LS120nz/OD-PT74-IC-Tester/docs/images/branding/image.png

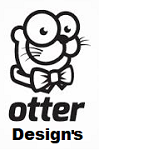
docs/images/branding/image.png
