LS120nz/OD-PT74-IC-Tester/docs/images/branding/png/otter_128.png

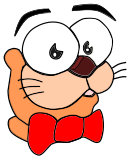
docs/images/branding/png/otter_128.png
