LS120nz/OD-PT74-IC-Tester/docs/images/branding/svga/OtterDesigns_FullColour.jpg

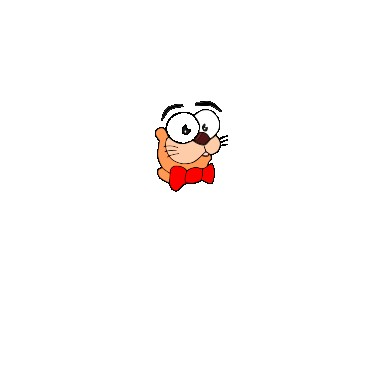
docs/images/branding/svga/OtterDesigns_FullColour.jpg
