LS120nz/OD-PT74-IC-Tester/docs/images/case labels/qr-back.png

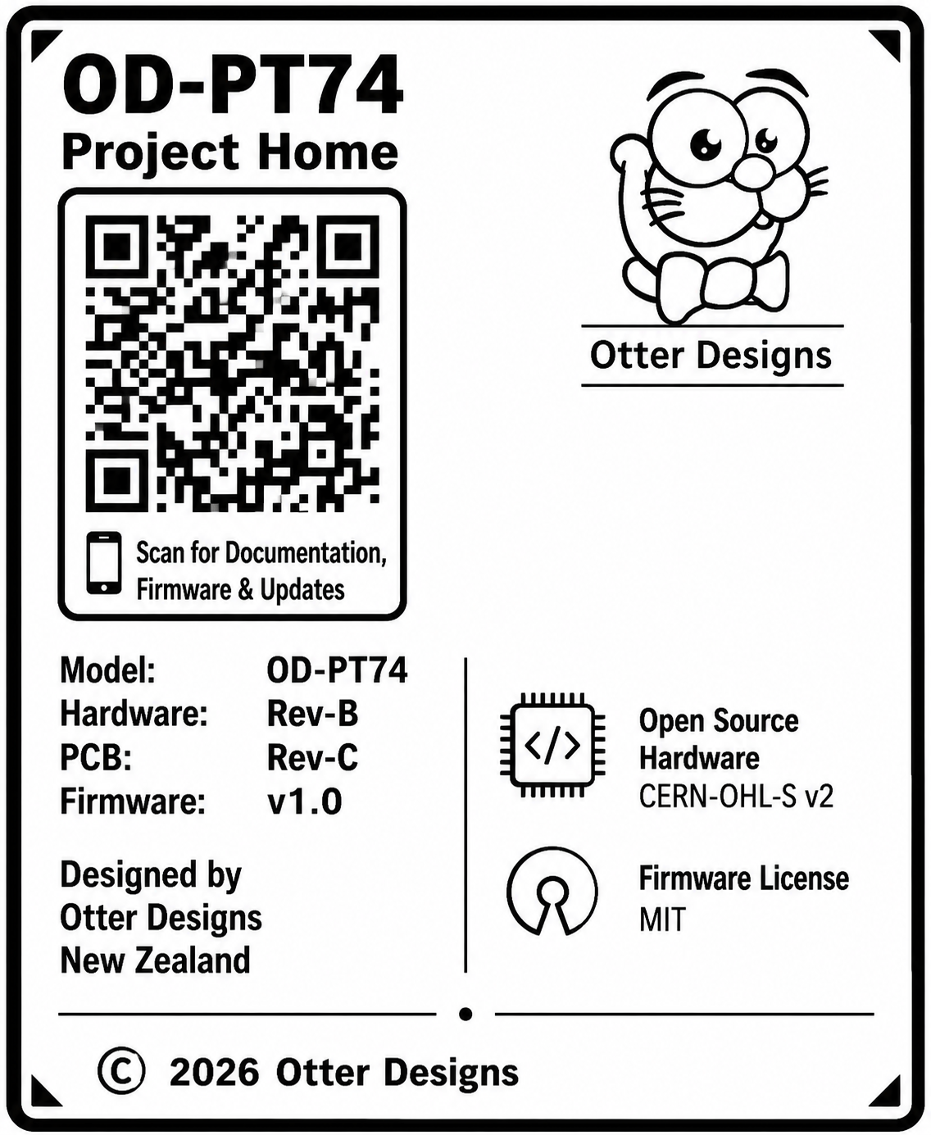
docs/images/case labels/qr-back.png
