LS120nz/OD-PT74-IC-Tester/docs/images/firmware/03-usb-settings.jpg

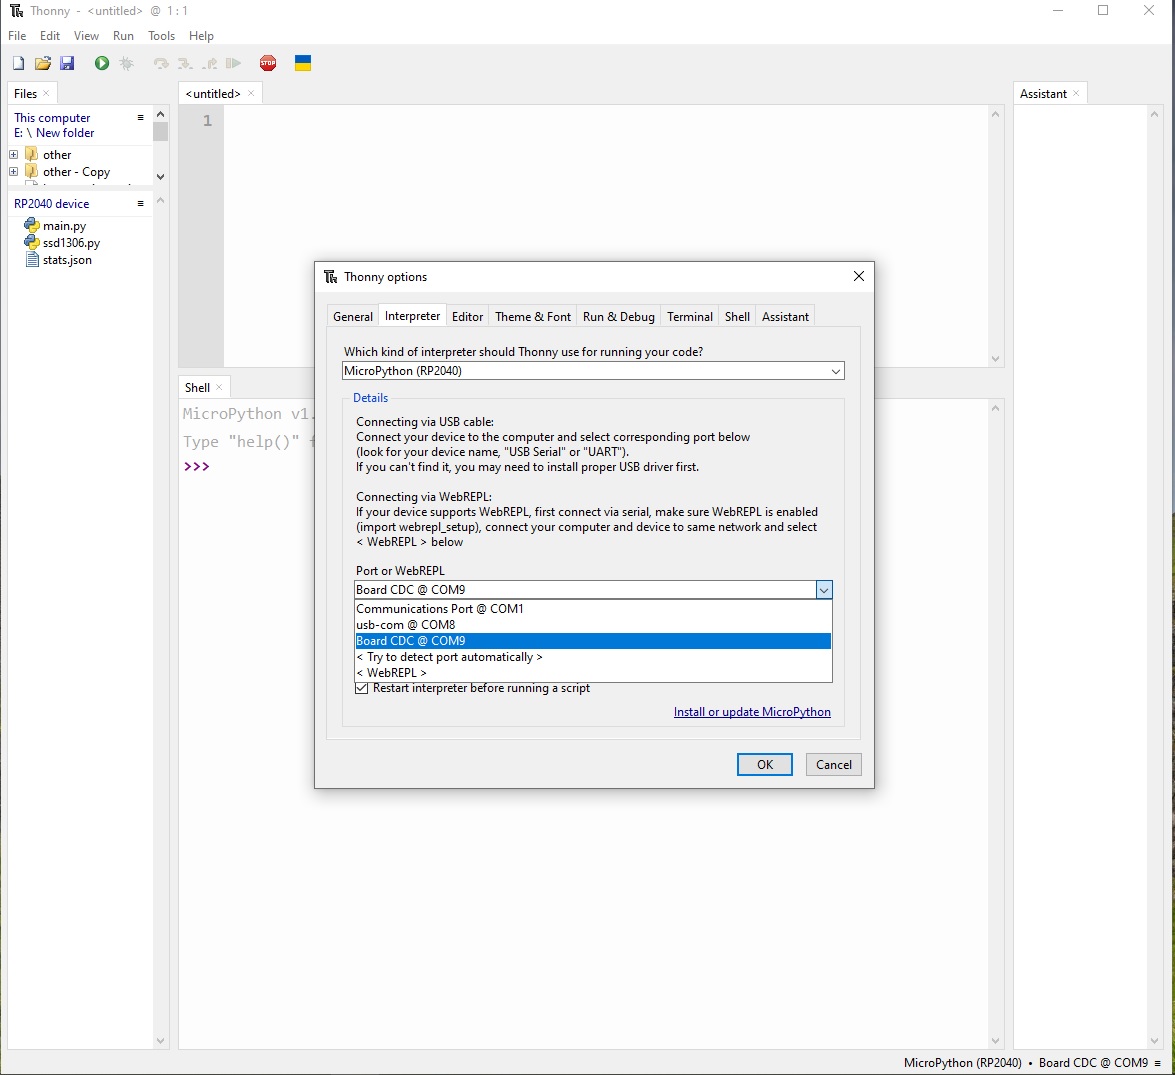
docs/images/firmware/03-usb-settings.jpg
