LS120nz/OD-PT74-IC-Tester/docs/images/firmware/24-files on PR2040.jpg

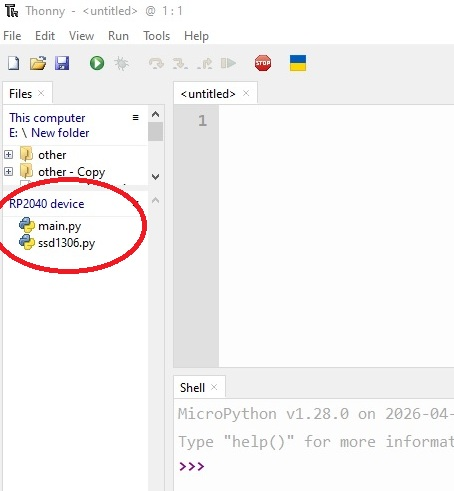
docs/images/firmware/24-files on PR2040.jpg
