LS120nz/OD-PT74-IC-Tester/docs/images/hardware/case label.jpg

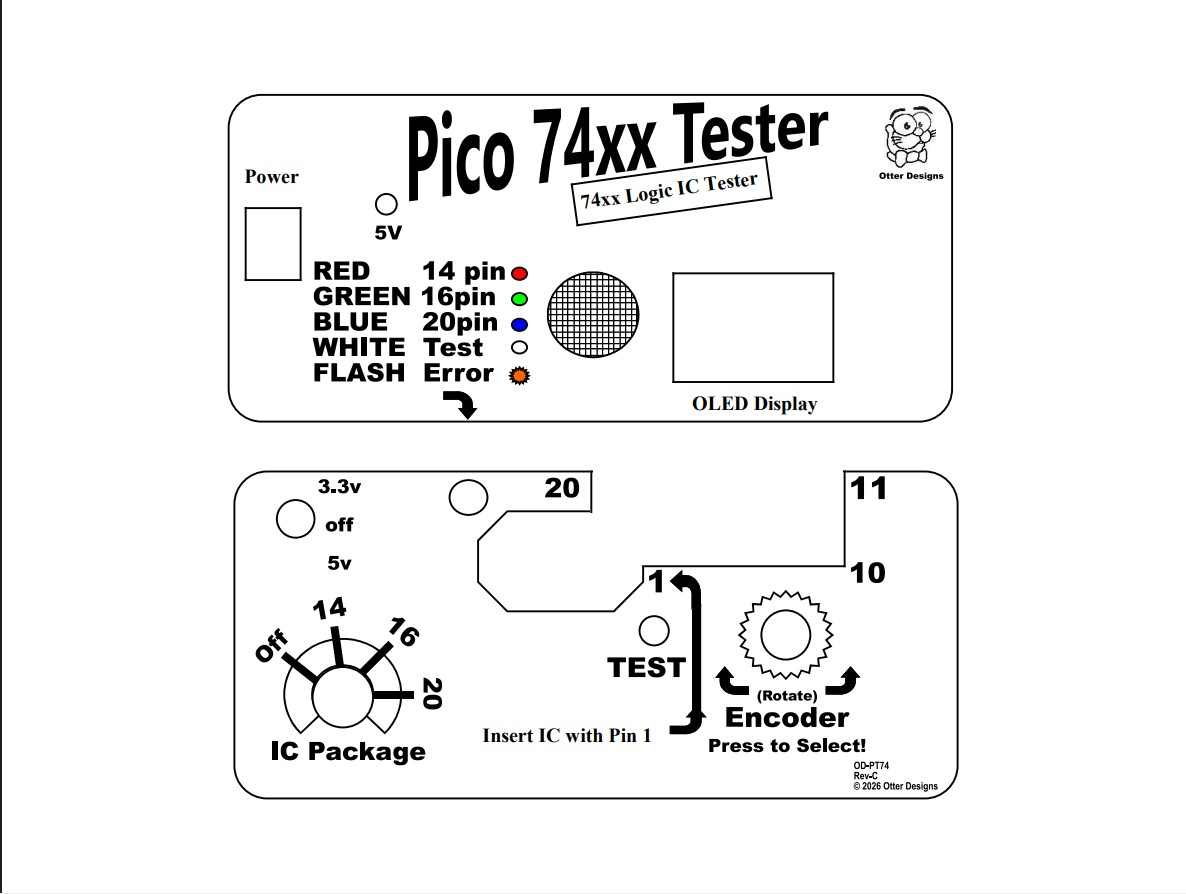
docs/images/hardware/case label.jpg
