LS120nz/OD-PT74-IC-Tester/docs/images/hardware/enclosure.jpg

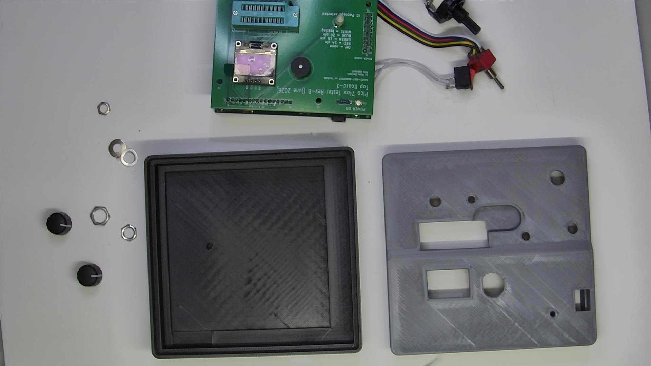
docs/images/hardware/enclosure.jpg
