LS120nz/OD-PT74-IC-Tester/docs/images/hardware/internal-view.jpg

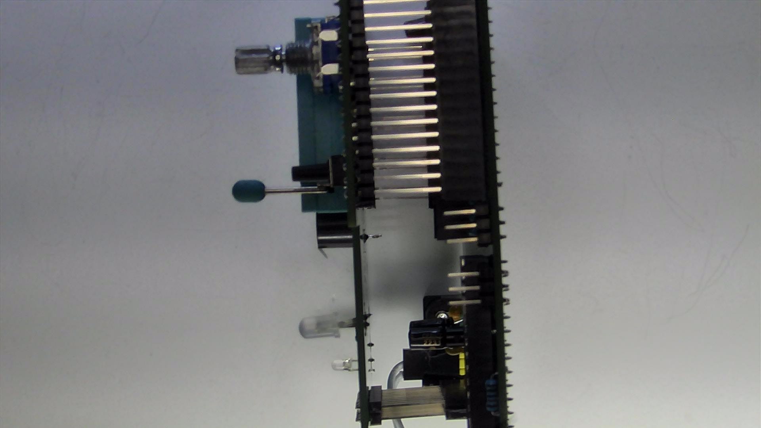
docs/images/hardware/internal-view.jpg
