LS120nz/OD-PT74-IC-Tester/hardware/OD-PT74 - Rev-C/Base Board/Images/OD-PT74_Rev-C_Base_Board-3D.png

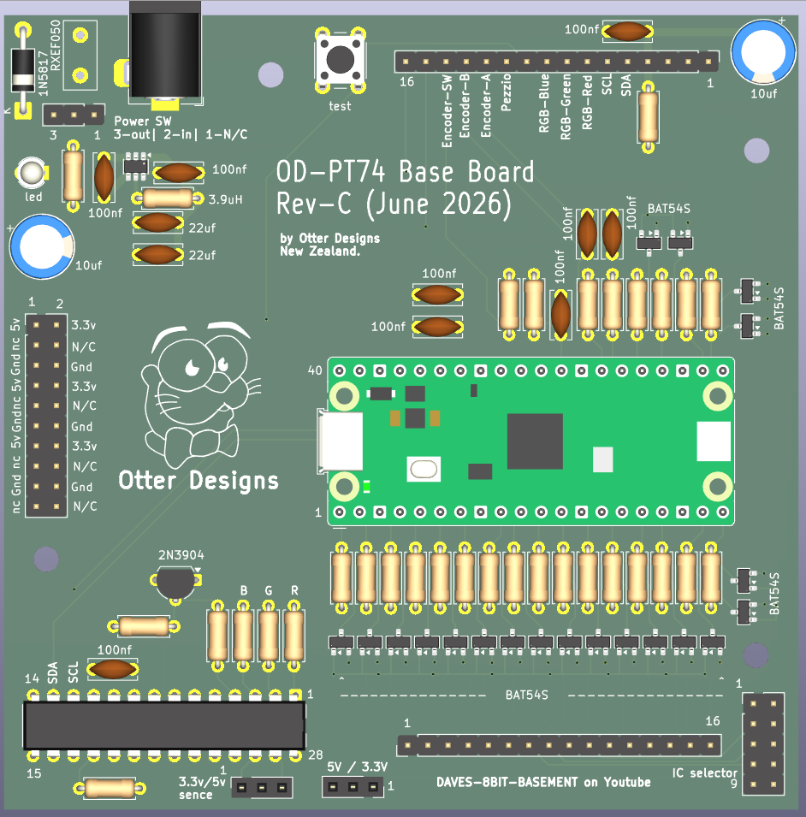
hardware/OD-PT74 - Rev-C/Base Board/Images/OD-PT74_Rev-C_Base_Board-3D.png
