LS120nz/OD-PT74-IC-Tester/hardware/OD-PT74 - Rev-C/Top Board/Images/3d top board.png

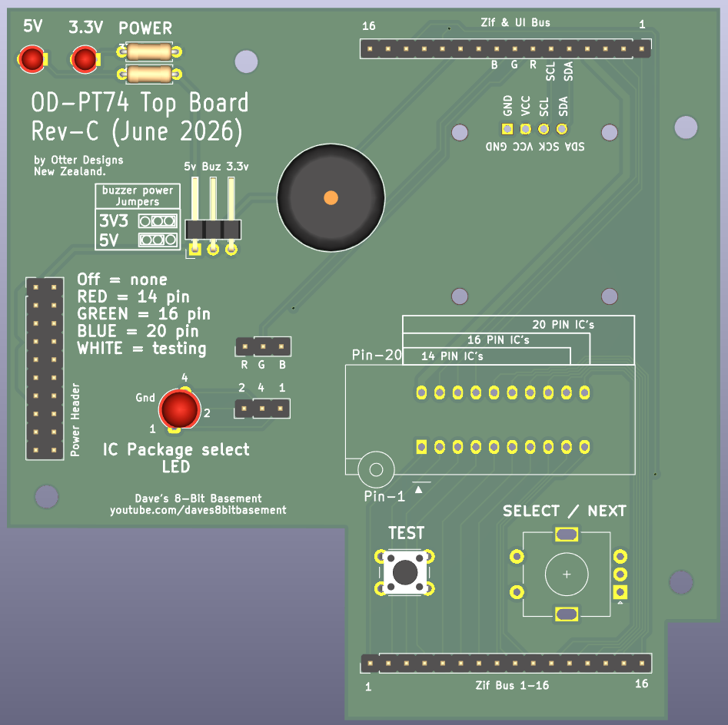
hardware/OD-PT74 - Rev-C/Top Board/Images/3d top board.png
