LS120nz/OD-PT74-IC-Tester/hardware/OD-PT74 - Rev-C/Top Board/Images/top board schematics.png

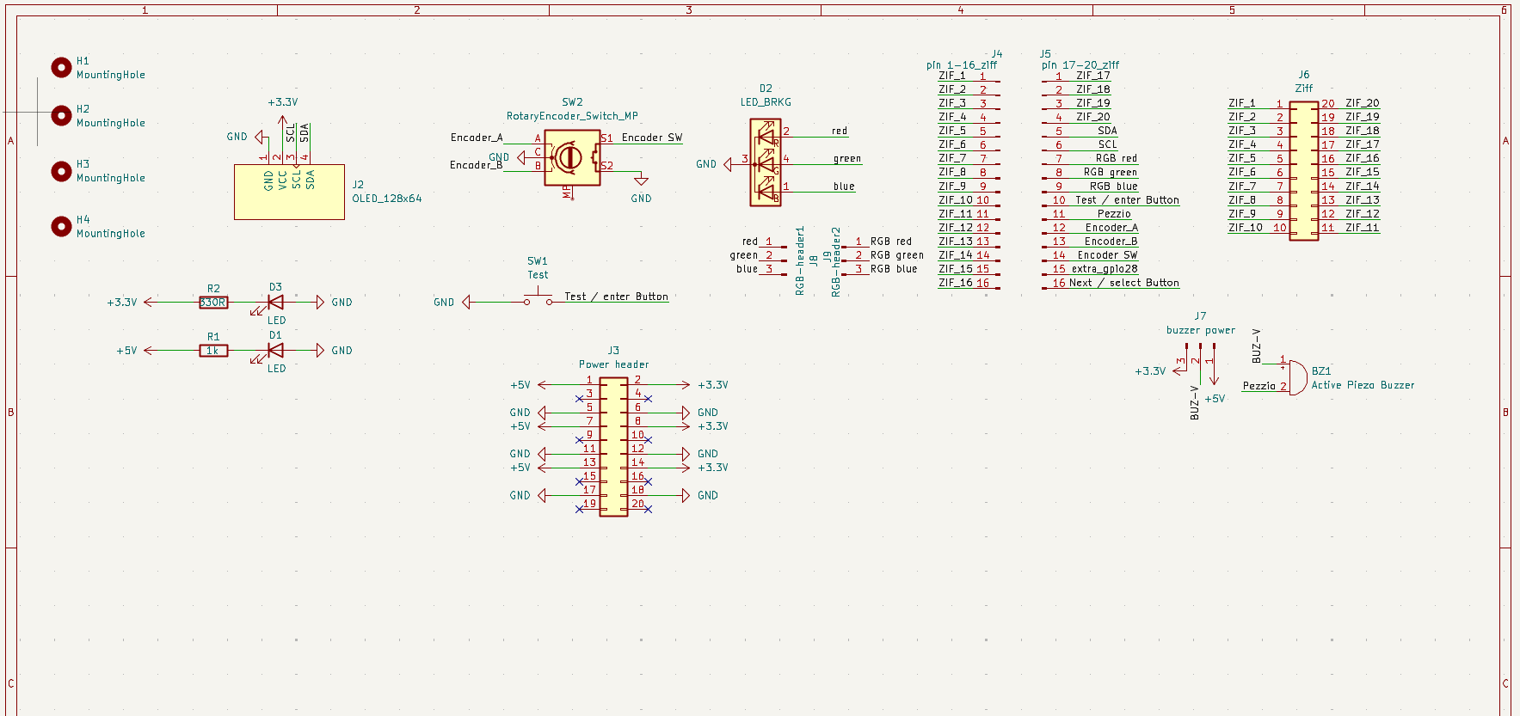
hardware/OD-PT74 - Rev-C/Top Board/Images/top board schematics.png
