LS120nz/OD-PT74-IC-Tester/images/enclosure/base-cad2.jpg

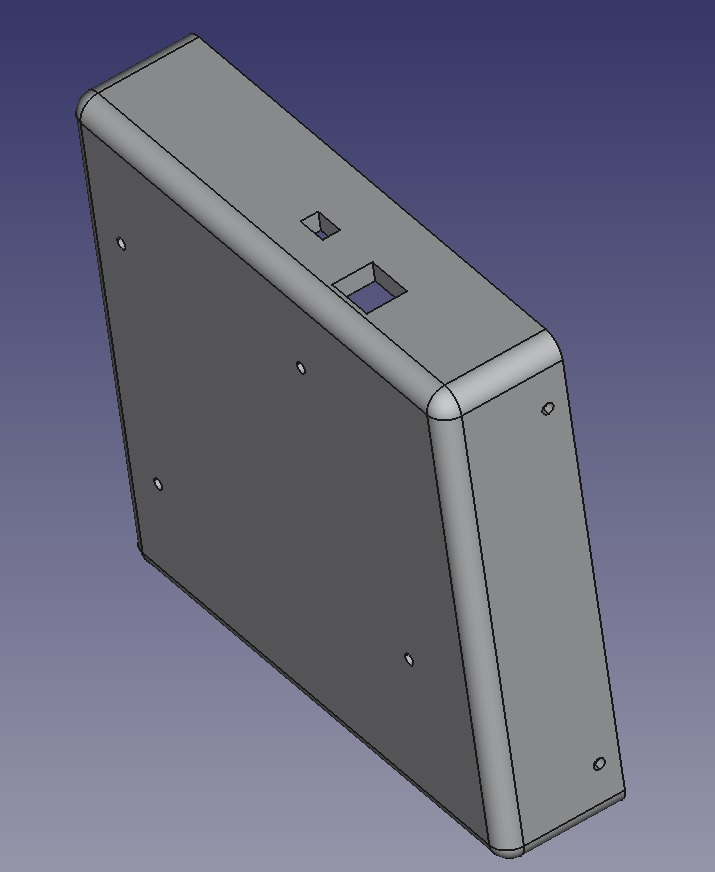
images/enclosure/base-cad2.jpg
