LS120nz/OD-PT74-IC-Tester/images/enclosure/base-cad.jpg

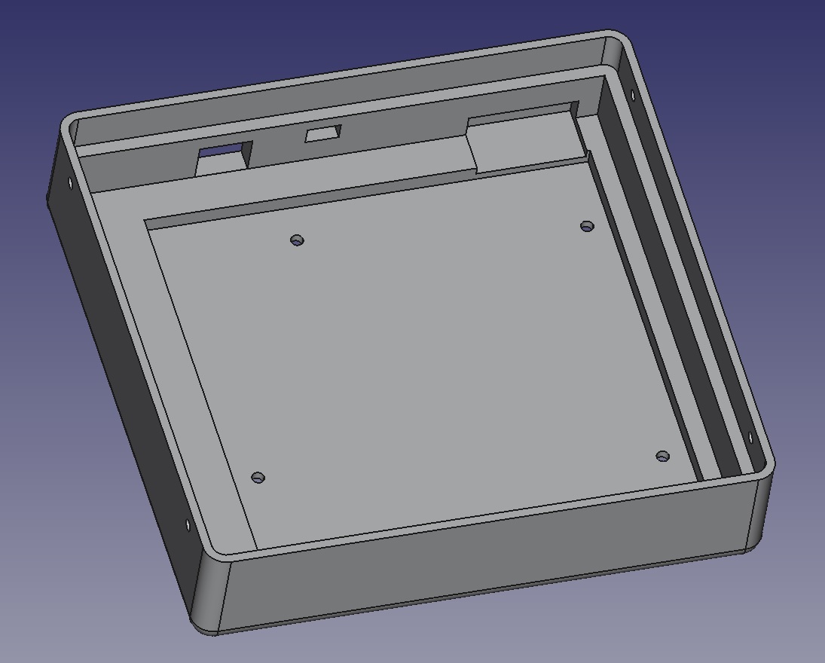
images/enclosure/base-cad.jpg
