LS120nz/OD-PT74-IC-Tester/images/enclosure/top-cad2.jpg

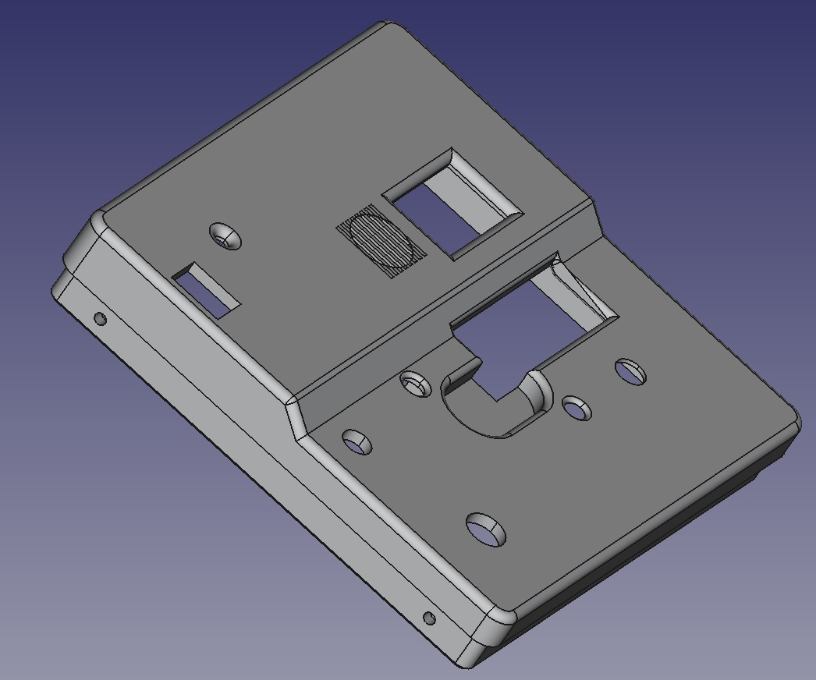
images/enclosure/top-cad2.jpg
