LS120nz/OD-PT74-IC-Tester/images/enclosure/top-cad3.jpg

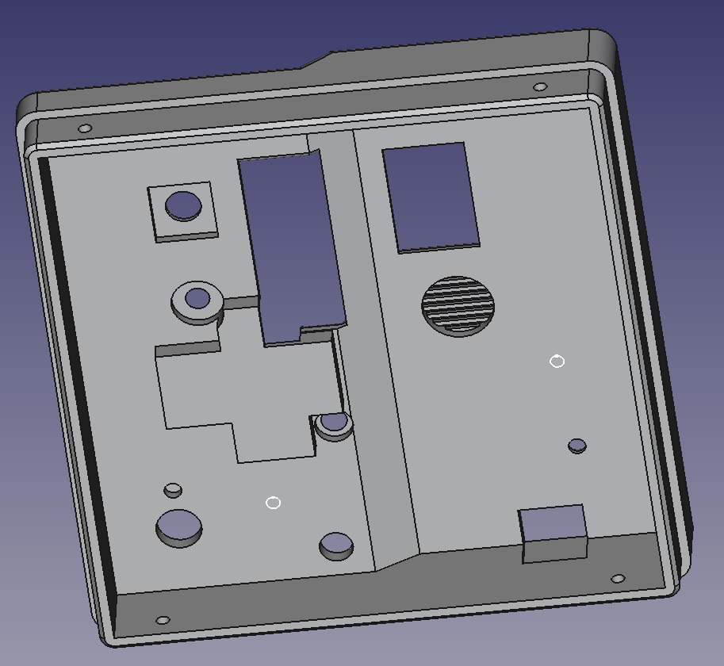
images/enclosure/top-cad3.jpg
