LS120nz/OD-PT74-IC-Tester/images/enclosure/top-cad.jpg

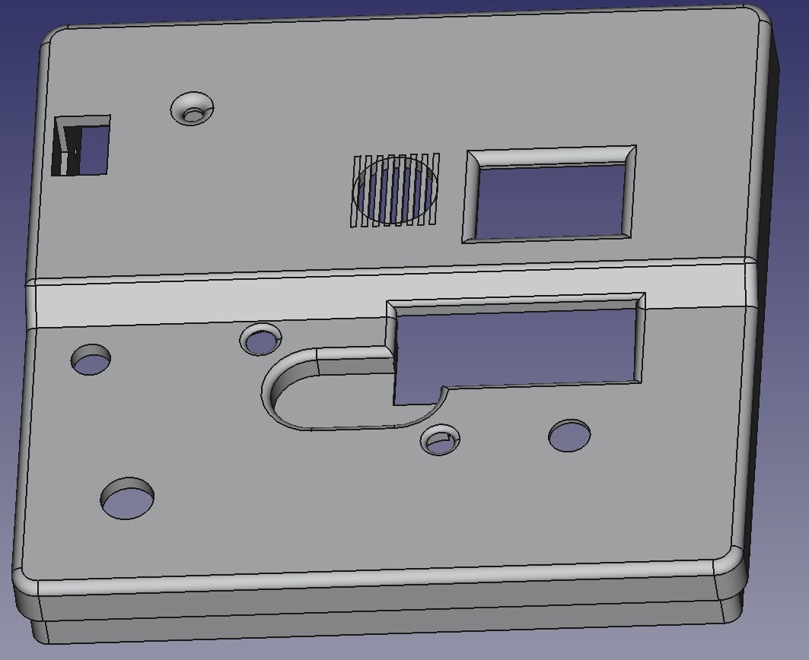
images/enclosure/top-cad.jpg
