LS120nz/OD-PT74-IC-Tester/images/pcb-back.jpg

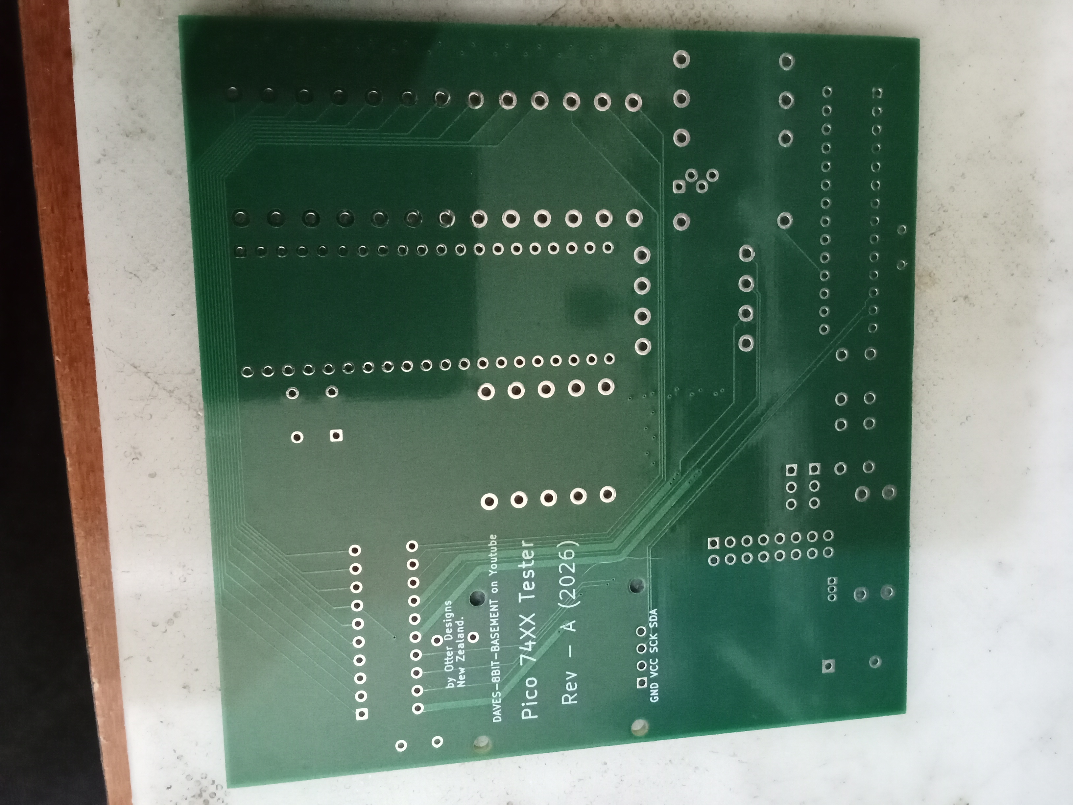
images/pcb-back.jpg
