LS120nz/OD-PT74-IC-Tester/images/pcb-front.jpg

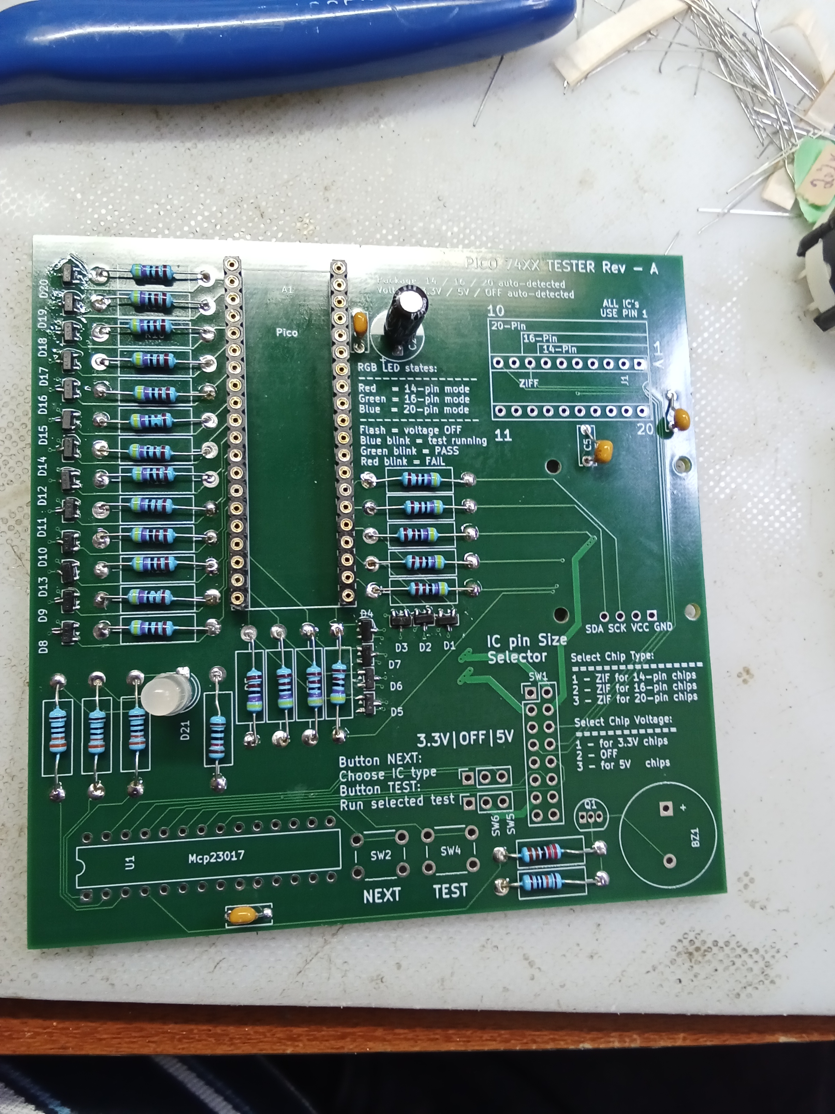
images/pcb-front.jpg
