LS120nz/OD-PT74-IC-Tester/images/RevB-3d-board-top.png

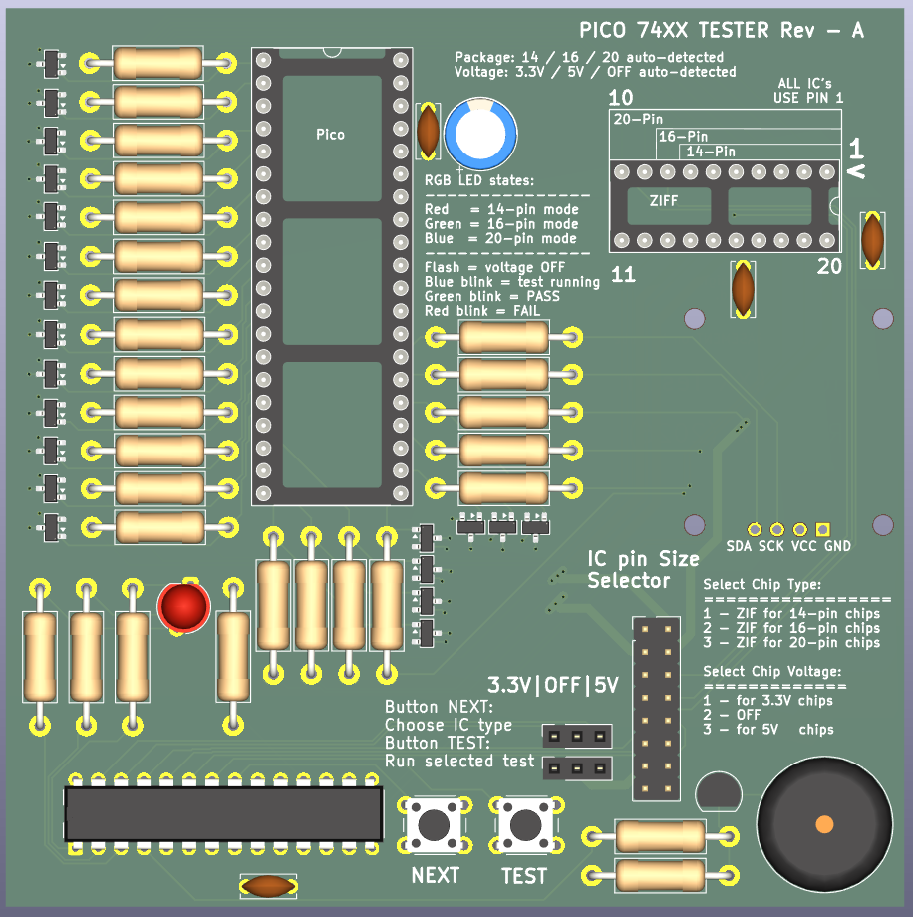
images/RevB-3d-board-top.png
