LS120nz/OD-PT74-IC-Tester/images/top-back-3d.png

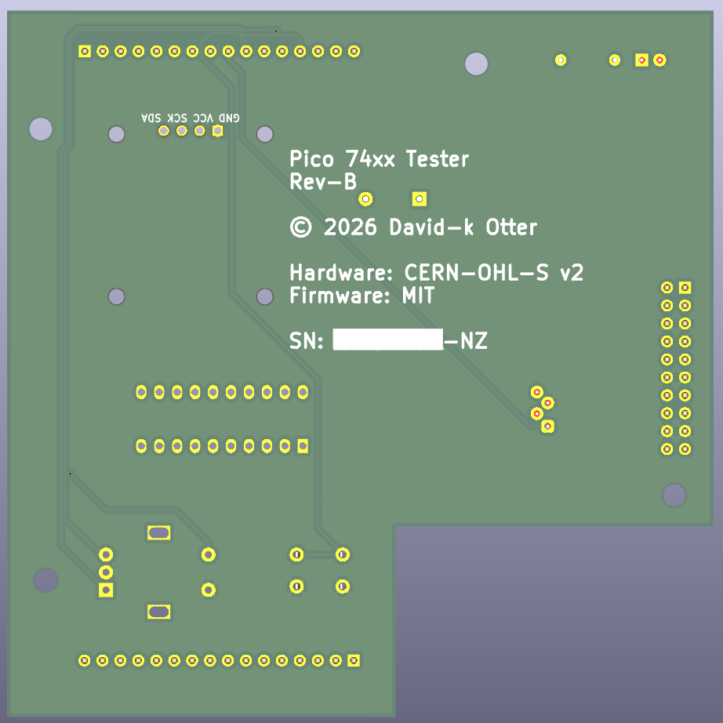
images/top-back-3d.png
