LS120nz/OD-PT74-IC-Tester/images/top-front-3d.png

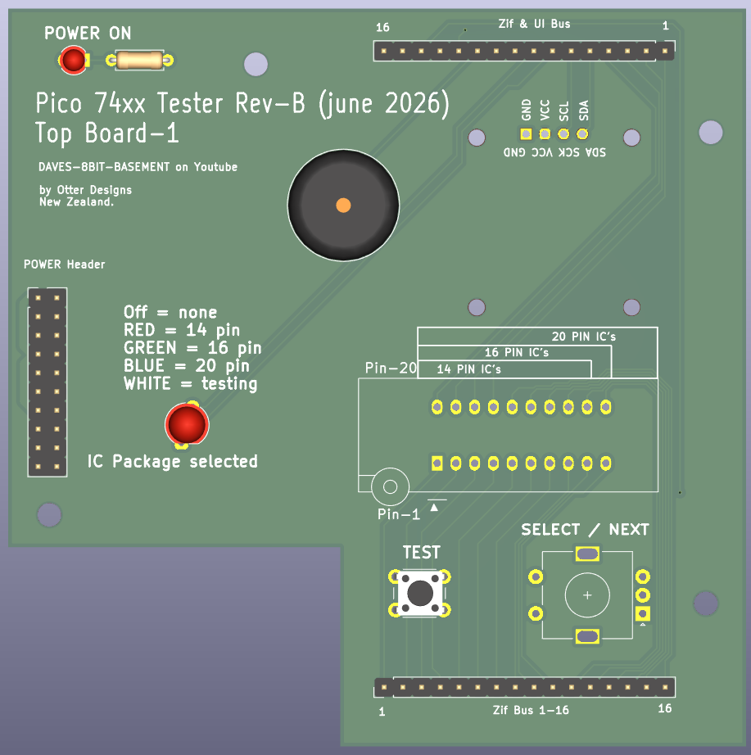
images/top-front-3d.png
