LS120nz/OD-PT74-IC-Tester/images/top-kicad-drawing.png

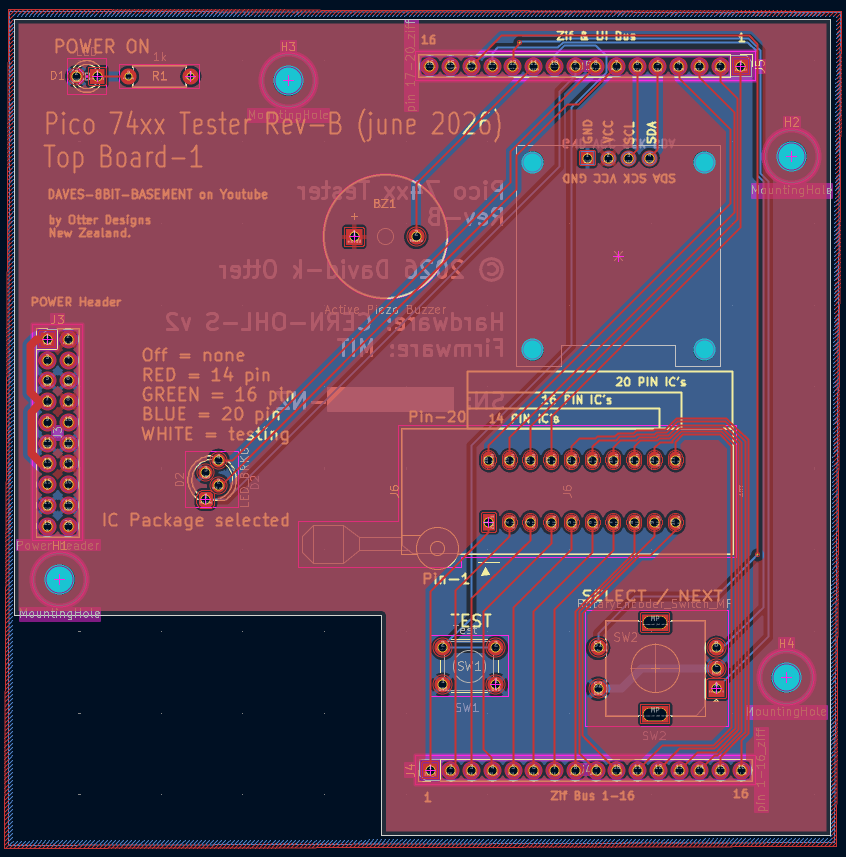
images/top-kicad-drawing.png
