LS120nz/OD-PT74-IC-Tester/docs/images/build/22-topboard-parts.jpg

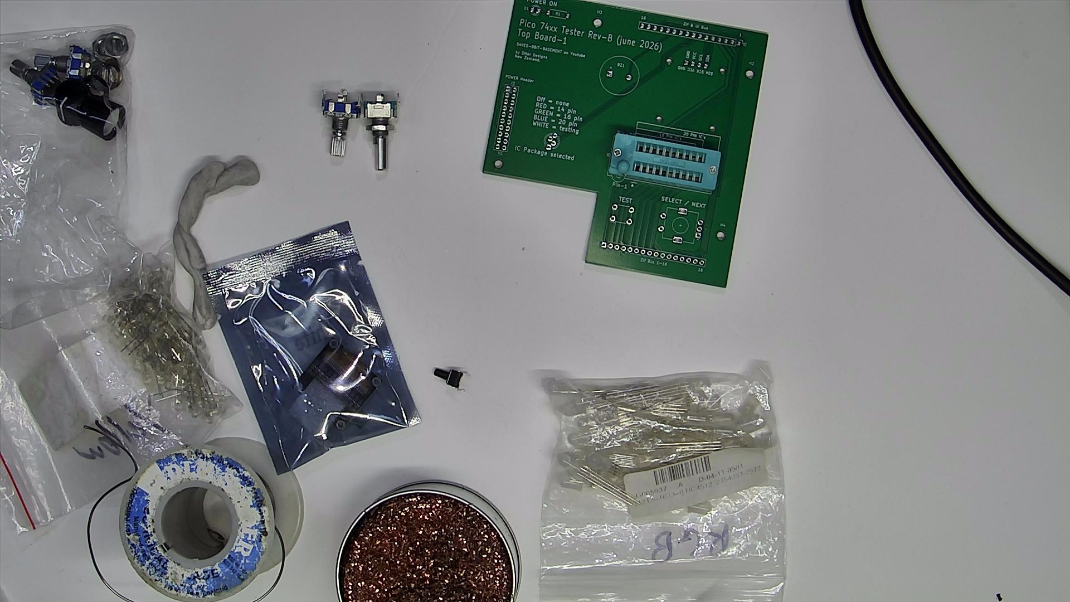
docs/images/build/22-topboard-parts.jpg
