LS120nz/OD-PT74-IC-Tester/docs/images/build/06-attach header pins.jpg

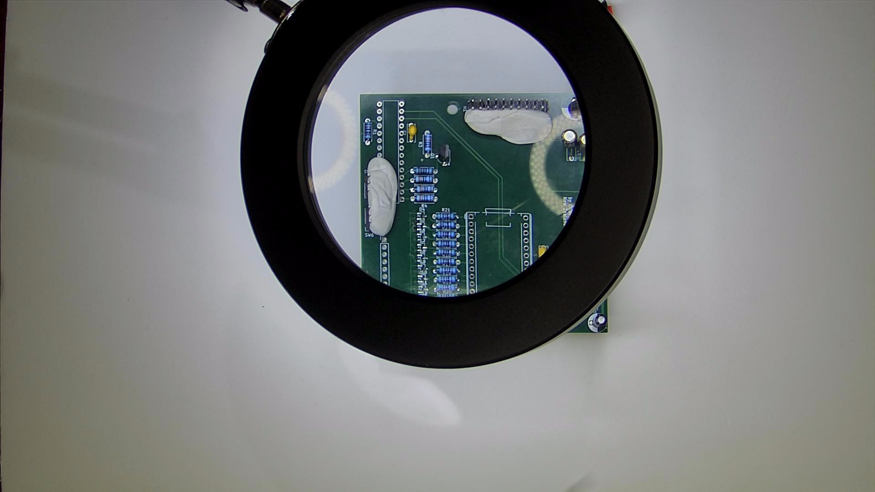
docs/images/build/06-attach header pins.jpg
