LS120nz/OD-PT74-IC-Tester/docs/images/build/08-baseboard-headers.jpg

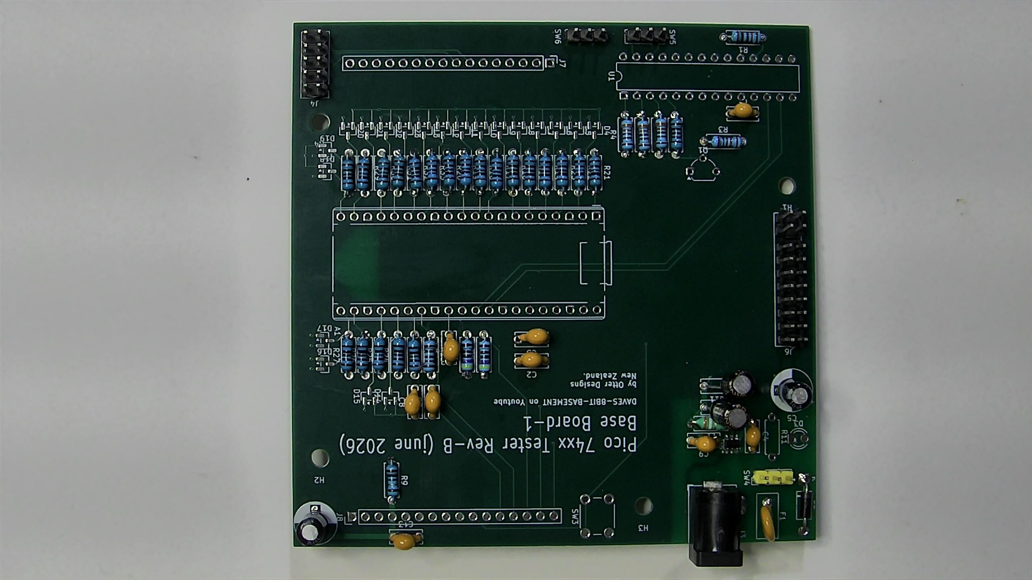
docs/images/build/08-baseboard-headers.jpg
