LS120nz/OD-PT74-IC-Tester/docs/images/build/09-first-bat-1.jpg

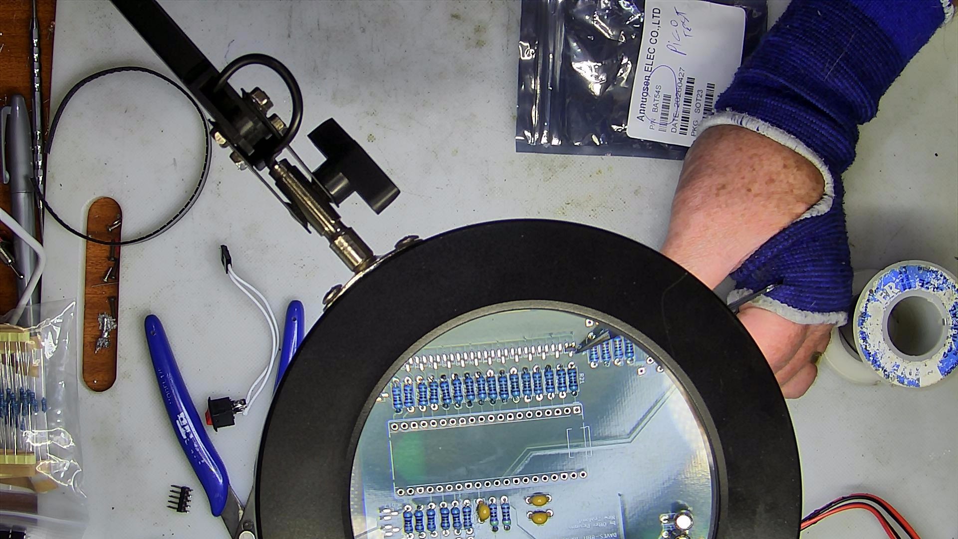
docs/images/build/09-first-bat-1.jpg
