LS120nz/OD-PT74-IC-Tester/docs/images/build/10-fist-bat-2.jpg

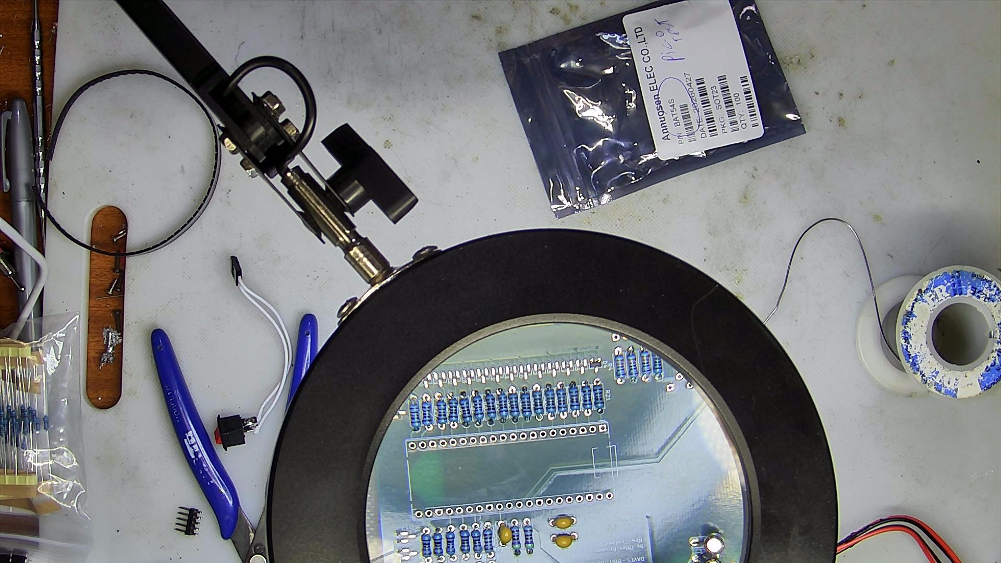
docs/images/build/10-fist-bat-2.jpg
