LS120nz/OD-PT74-IC-Tester/docs/images/build/11-bat-4.jpg

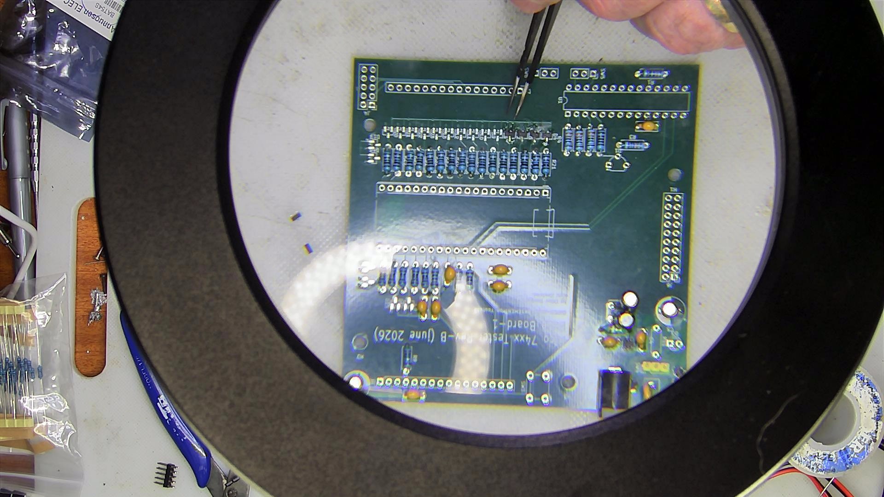
docs/images/build/11-bat-4.jpg
