LS120nz/OD-PT74-IC-Tester/docs/images/build/13-bat-attach-2_3.jpg

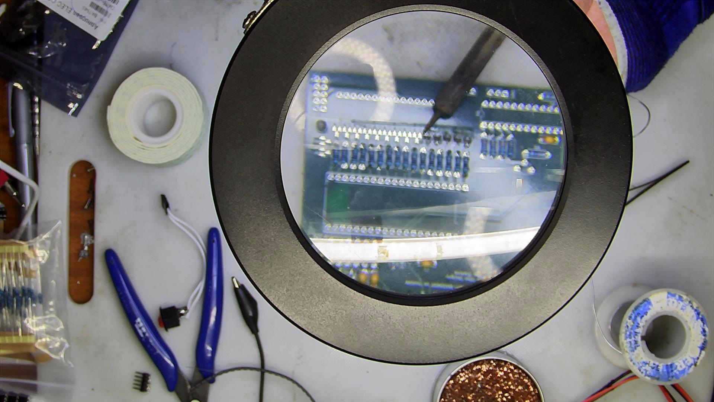
docs/images/build/13-bat-attach-2_3.jpg
