LS120nz/OD-PT74-IC-Tester/docs/images/build/14-bat-5-strighten.jpg

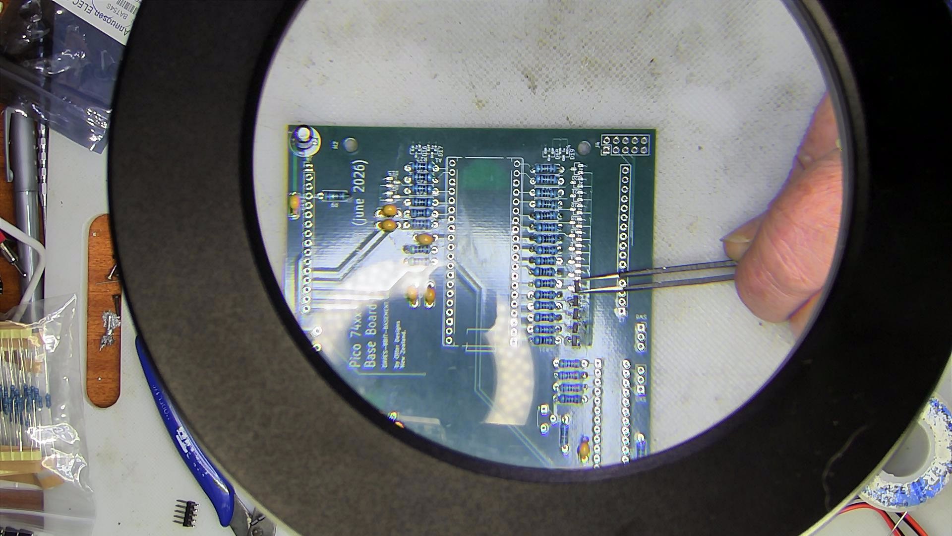
docs/images/build/14-bat-5-strighten.jpg
