LS120nz/OD-PT74-IC-Tester/docs/images/build/15-baseboard-most-bats.jpg

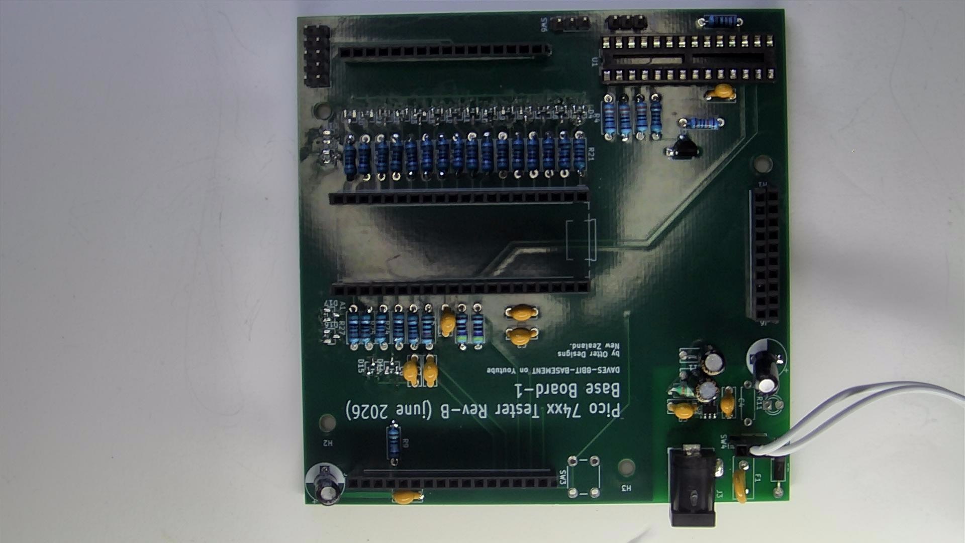
docs/images/build/15-baseboard-most-bats.jpg
