LS120nz/OD-PT74-IC-Tester/docs/images/build/21-blank-topboard.jpg

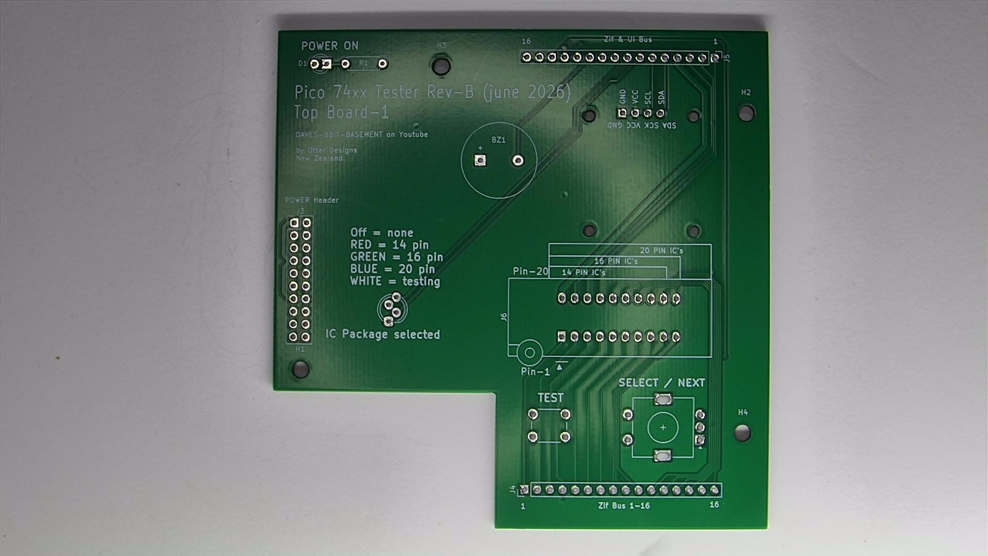
docs/images/build/21-blank-topboard.jpg
