LS120nz/OD-PT74-IC-Tester/docs/images/build/23-topboard-zif-solder.jpg

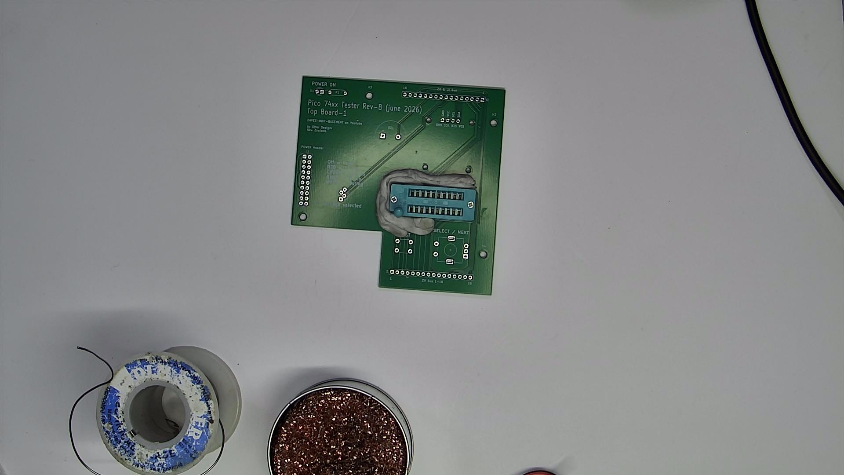
docs/images/build/23-topboard-zif-solder.jpg
