LS120nz/OD-PT74-IC-Tester/docs/images/build/24-topboard-rgb.jpg

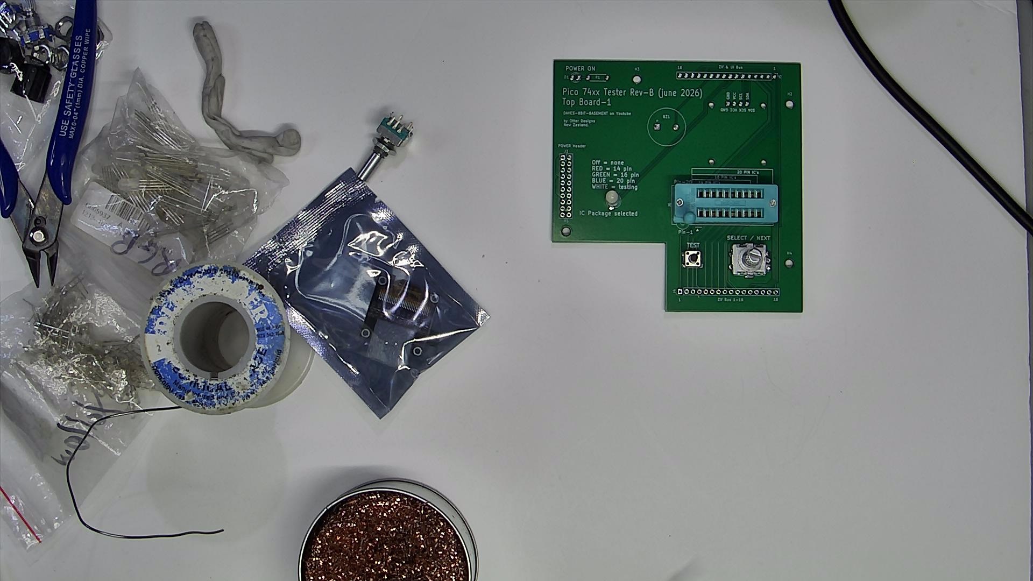
docs/images/build/24-topboard-rgb.jpg
