LS120nz/OD-PT74-IC-Tester/docs/images/build/26-oled-tape.jpg

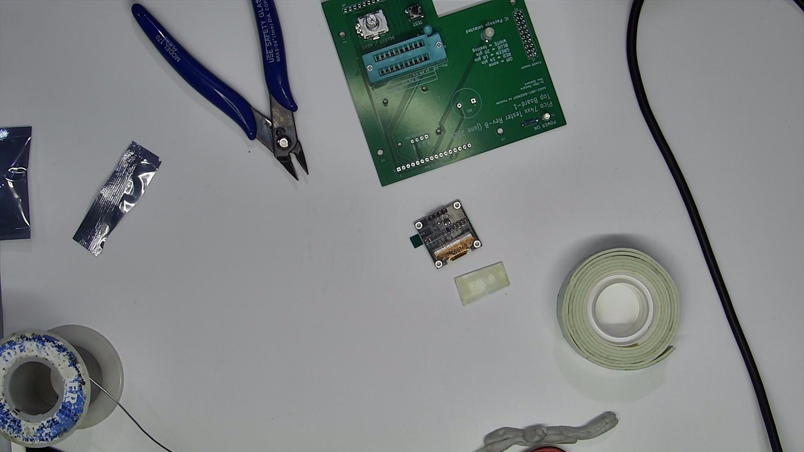
docs/images/build/26-oled-tape.jpg
