LS120nz/OD-PT74-IC-Tester/docs/images/build/27-oled-mount-tap.jpg

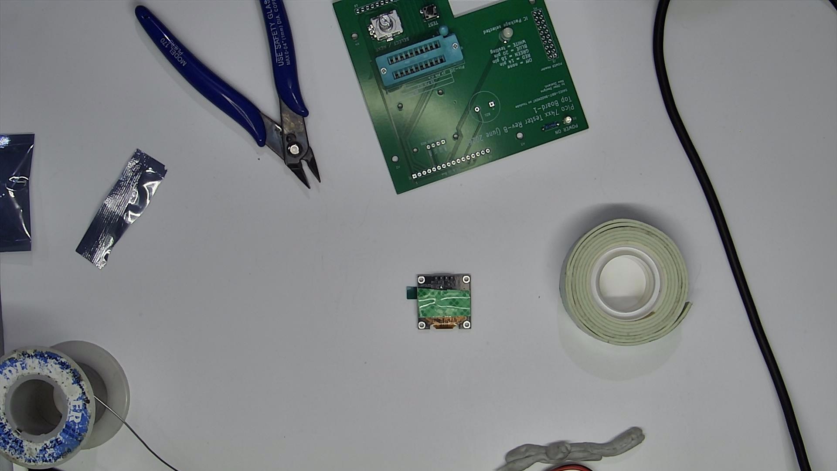
docs/images/build/27-oled-mount-tap.jpg
