LS120nz/OD-PT74-IC-Tester/docs/images/build/28-oled-side-view.jpg

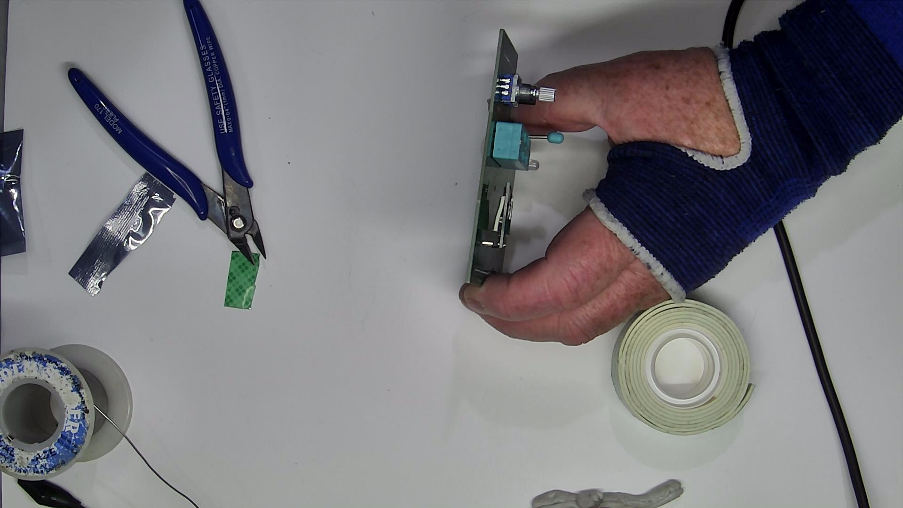
docs/images/build/28-oled-side-view.jpg
