LS120nz/OD-PT74-IC-Tester/docs/images/build/29-oled-side-mount.jpg

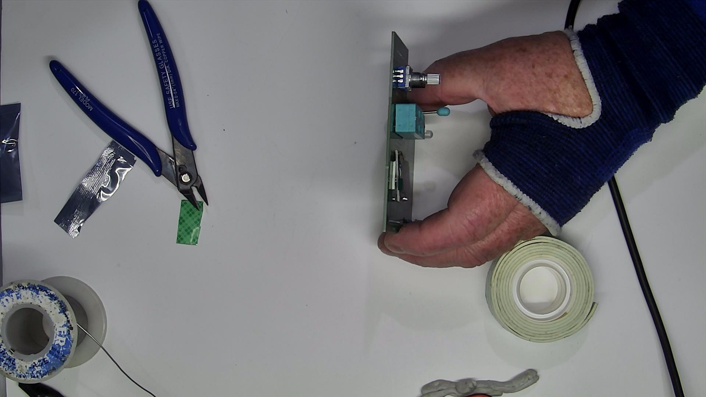
docs/images/build/29-oled-side-mount.jpg
