LS120nz/OD-PT74-IC-Tester/docs/images/build/30-power-led.jpg

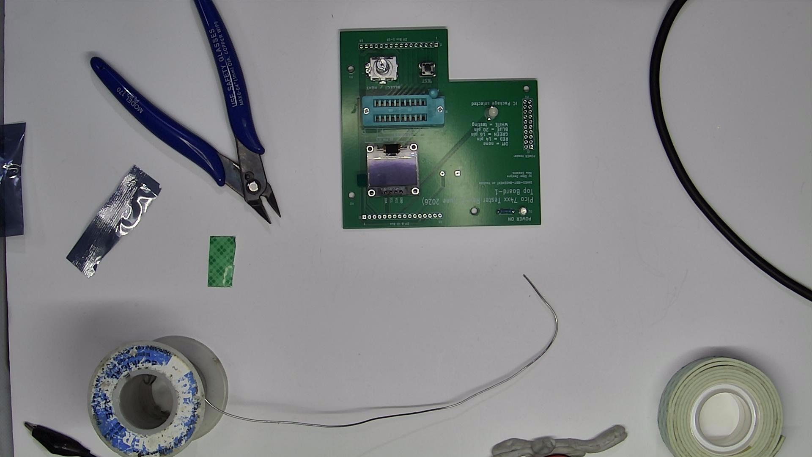
docs/images/build/30-power-led.jpg
