LS120nz/OD-PT74-IC-Tester/docs/images/build/31-topboard-header-aligen.jpg

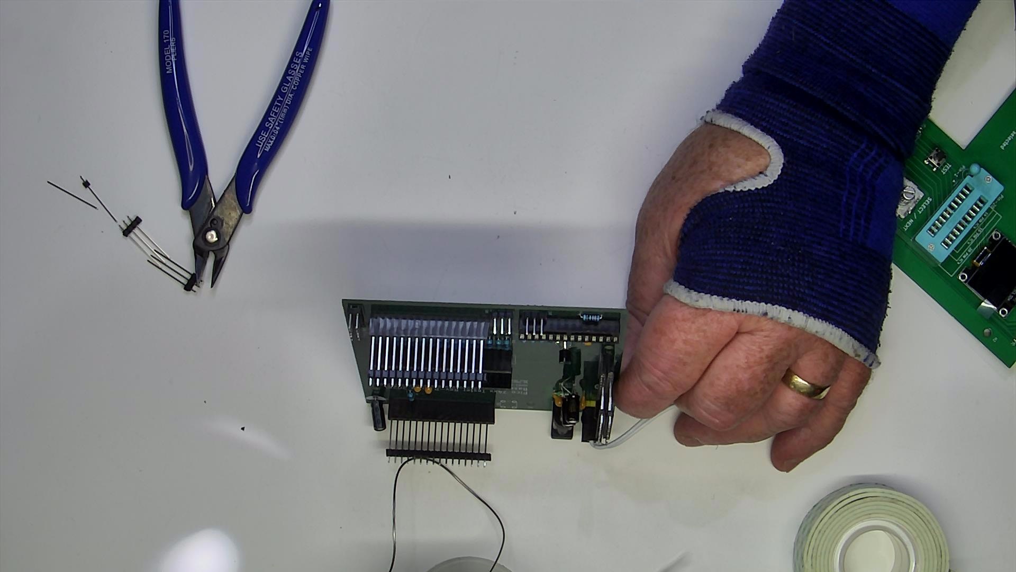
docs/images/build/31-topboard-header-aligen.jpg
