LS120nz/OD-PT74-IC-Tester/docs/images/build/32-topboard-hearer-aligen2.jpg

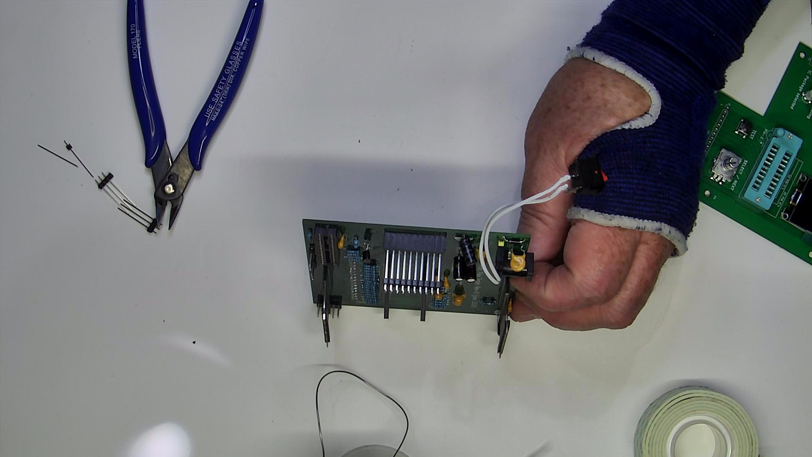
docs/images/build/32-topboard-hearer-aligen2.jpg
