LS120nz/OD-PT74-IC-Tester/docs/images/build/33-topboard aligen-on-pins.jpg

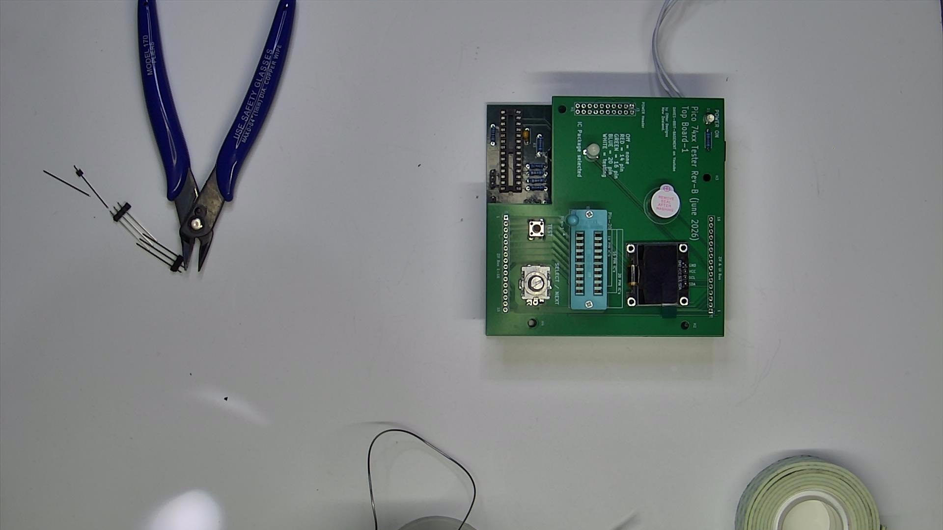
docs/images/build/33-topboard aligen-on-pins.jpg
