LS120nz/OD-PT74-IC-Tester/docs/images/build/34-topboard-buzzer-and-pins soldered.jpg

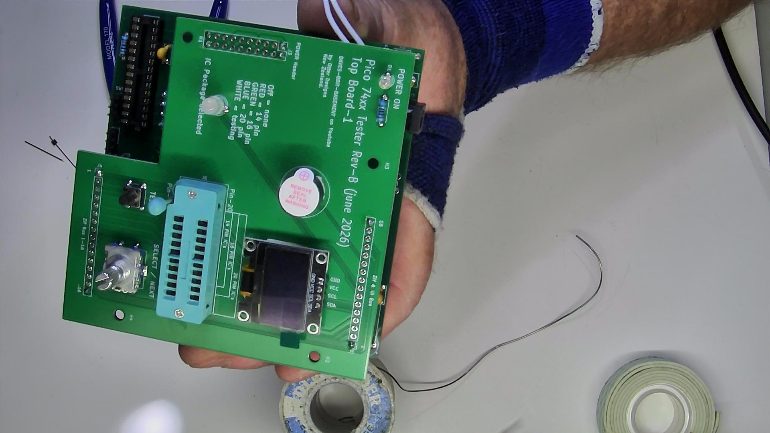
docs/images/build/34-topboard-buzzer-and-pins soldered.jpg
