LS120nz/OD-PT74-IC-Tester/docs/images/build/36-bottom-topboard.jpg

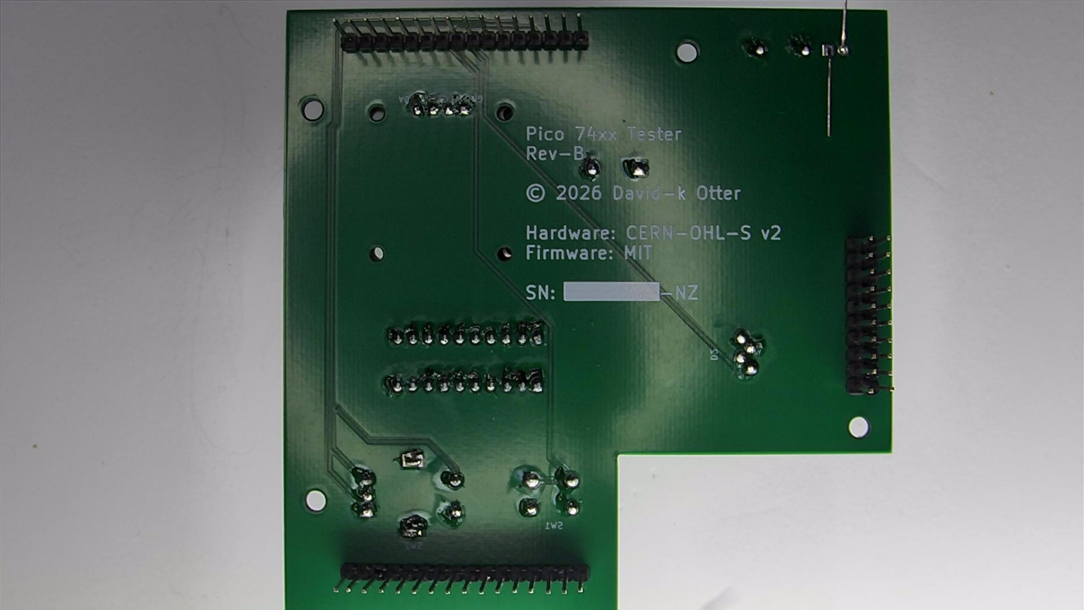
docs/images/build/36-bottom-topboard.jpg
