LS120nz/OD-PT74-IC-Tester/docs/images/build/38-selector-cables.jpg

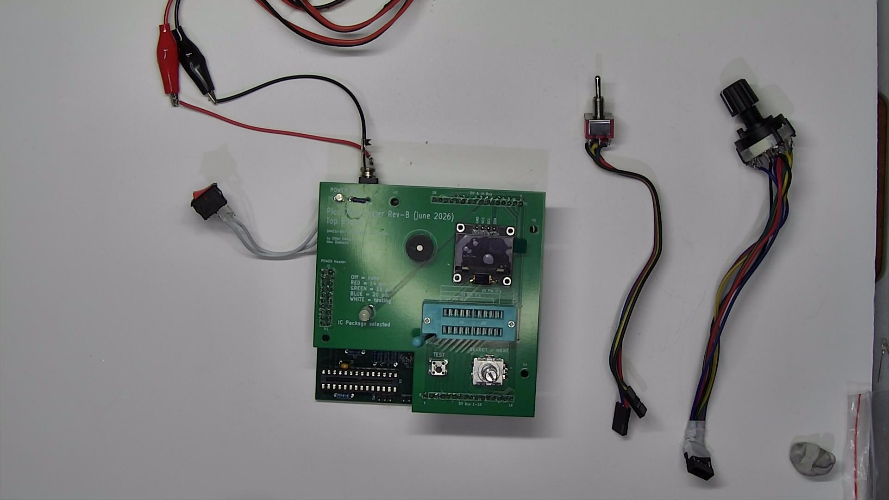
docs/images/build/38-selector-cables.jpg
