LS120nz/OD-PT74-IC-Tester/docs/images/build/39-selector-cables-closeup.jpg

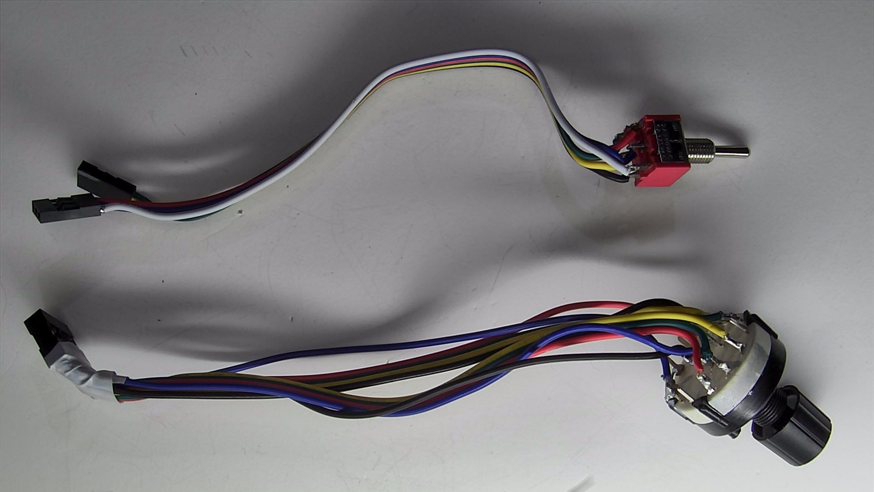
docs/images/build/39-selector-cables-closeup.jpg
