LS120nz/OD-PT74-IC-Tester/docs/images/build/40-baseboard-plugged-up.jpg

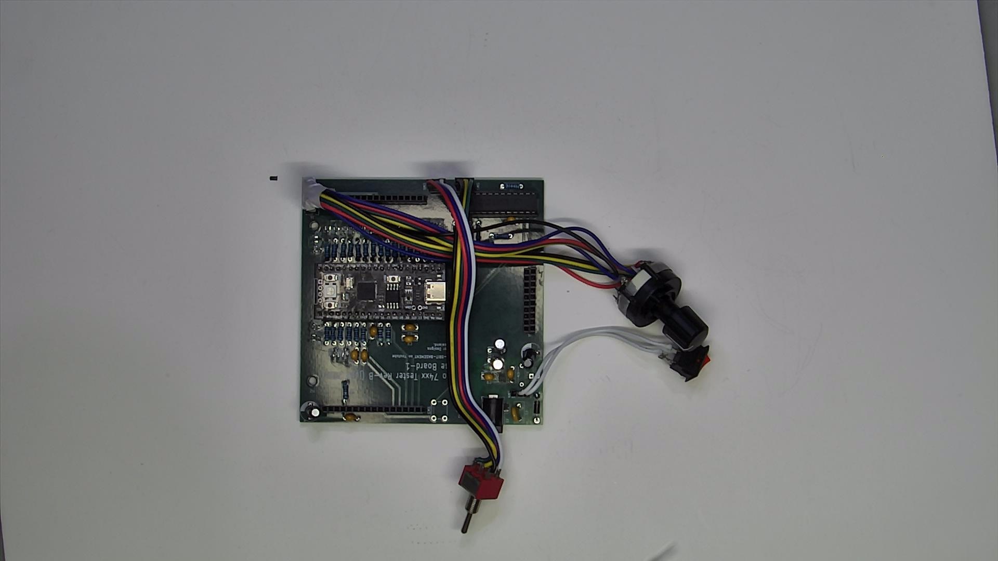
docs/images/build/40-baseboard-plugged-up.jpg
