LS120nz/OD-PT74-IC-Tester/docs/images/build/41-baseboard-plugged-up-side.jpg

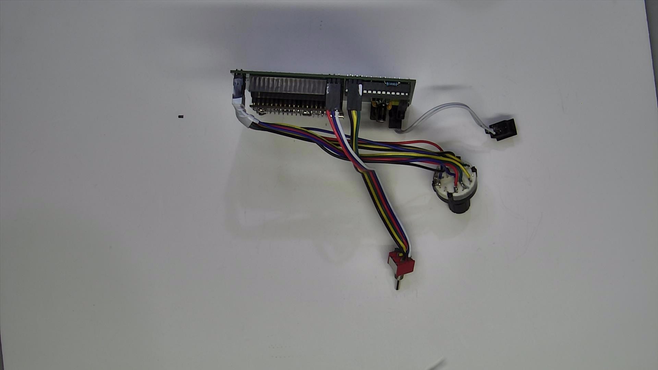
docs/images/build/41-baseboard-plugged-up-side.jpg
