LS120nz/OD-PT74-IC-Tester/docs/images/build/42-power-switch-in-case.jpg

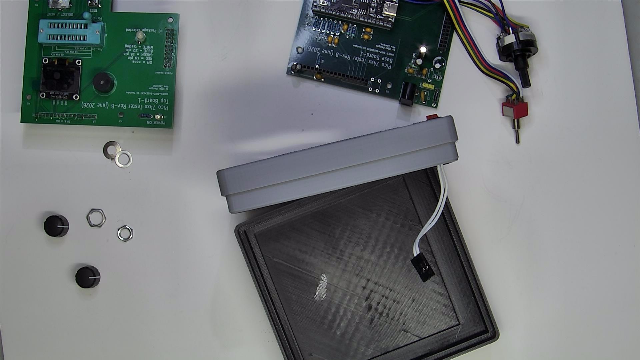
docs/images/build/42-power-switch-in-case.jpg
