LS120nz/OD-PT74-IC-Tester/docs/images/build/43-selector-align-hole-case.jpg

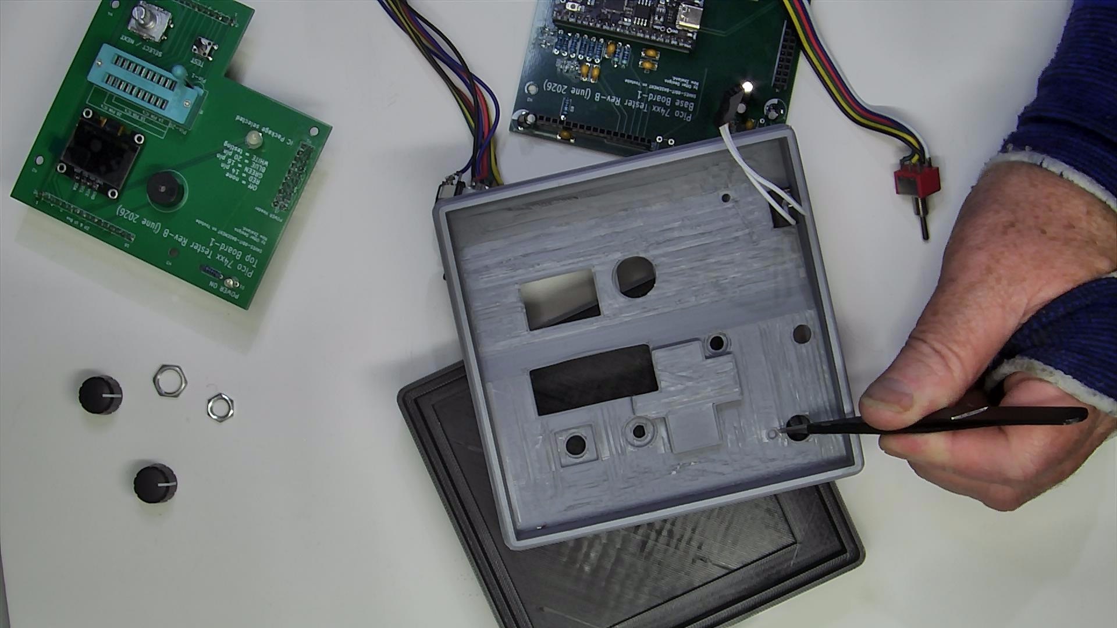
docs/images/build/43-selector-align-hole-case.jpg
