LS120nz/OD-PT74-IC-Tester/docs/images/build/44-selector-pin-dot.jpg

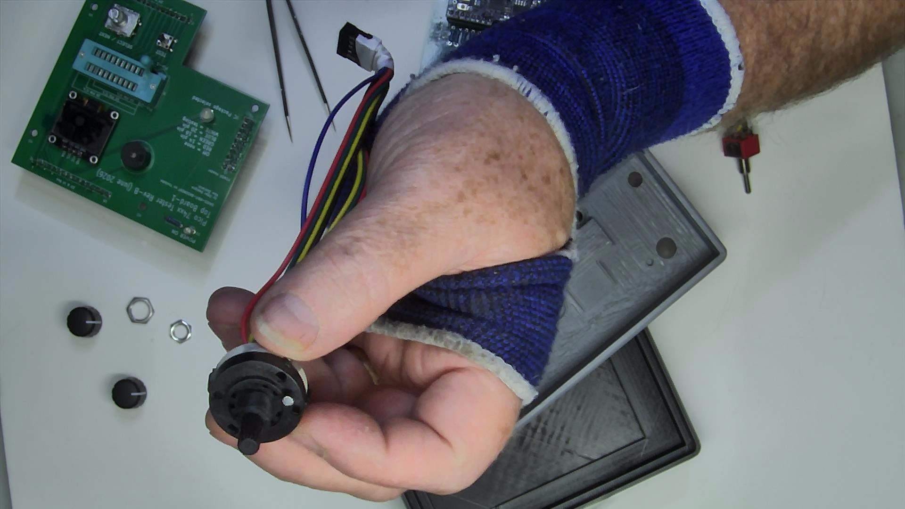
docs/images/build/44-selector-pin-dot.jpg
