LS120nz/OD-PT74-IC-Tester/docs/images/build/45-cable-management.jpg

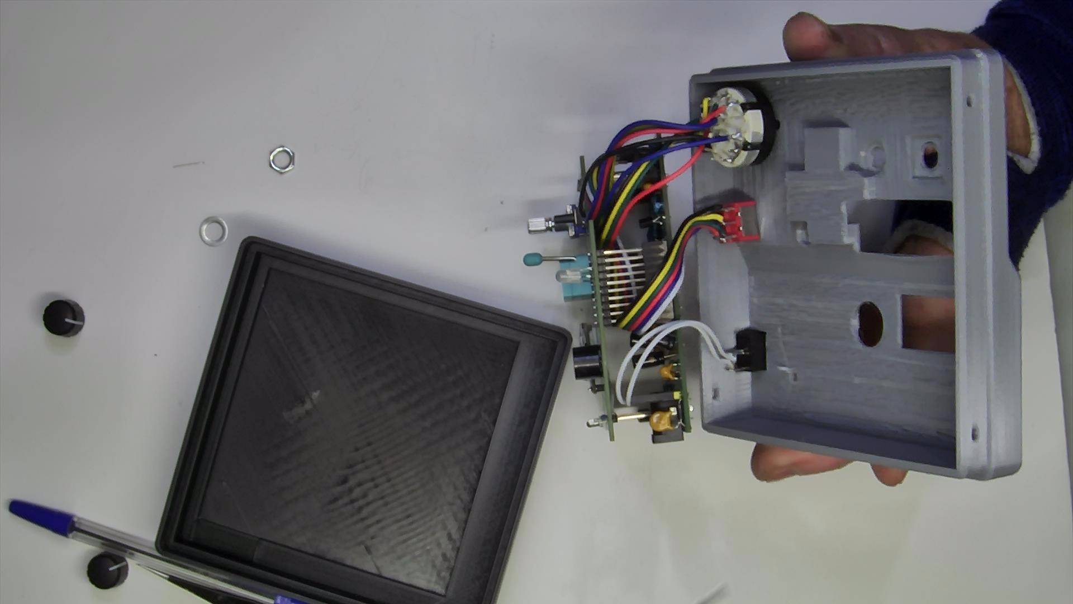
docs/images/build/45-cable-management.jpg
