LS120nz/OD-PT74-IC-Tester/docs/images/build/46-full-stack-boards-top.jpg

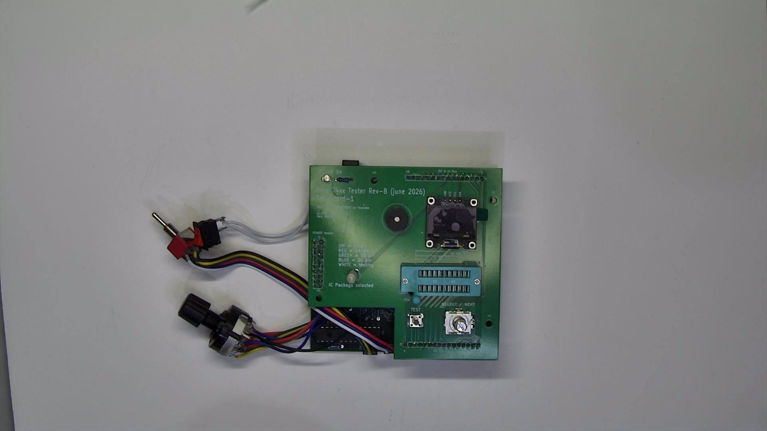
docs/images/build/46-full-stack-boards-top.jpg
