LS120nz/OD-PT74-IC-Tester/docs/images/build/50-baseboard-power-jack-case-hole.jpg

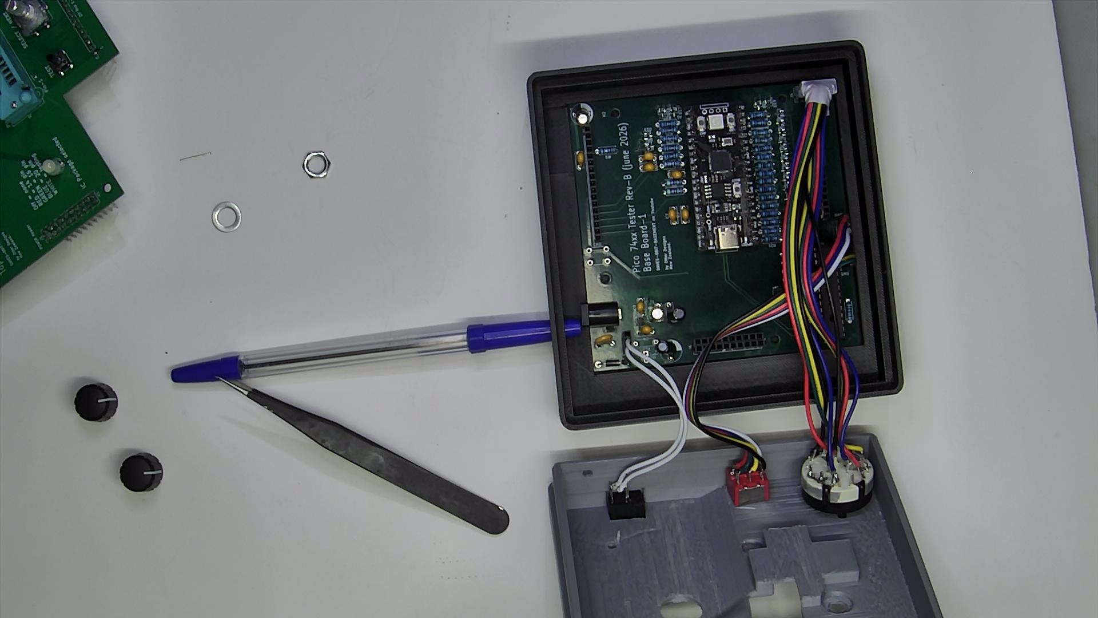
docs/images/build/50-baseboard-power-jack-case-hole.jpg
