LS120nz/OD-PT74-IC-Tester/docs/images/build/52-switch-selector-power_select-top-case.jpg

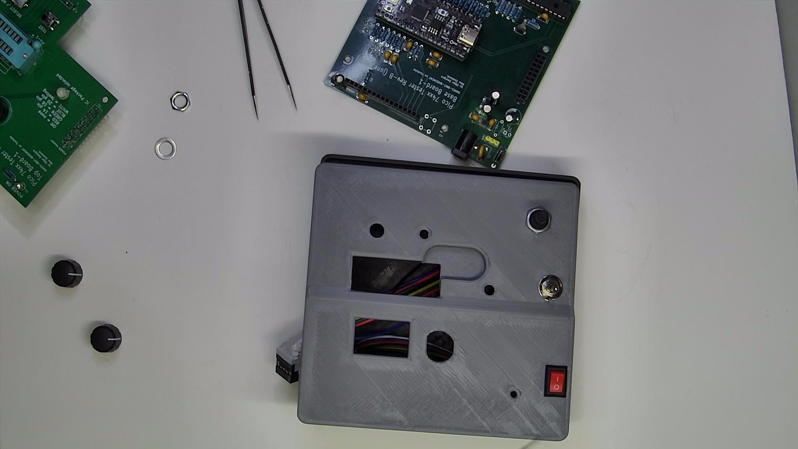
docs/images/build/52-switch-selector-power_select-top-case.jpg
