LS120nz/OD-PT74-IC-Tester/docs/images/build/53-top-case-close.jpg

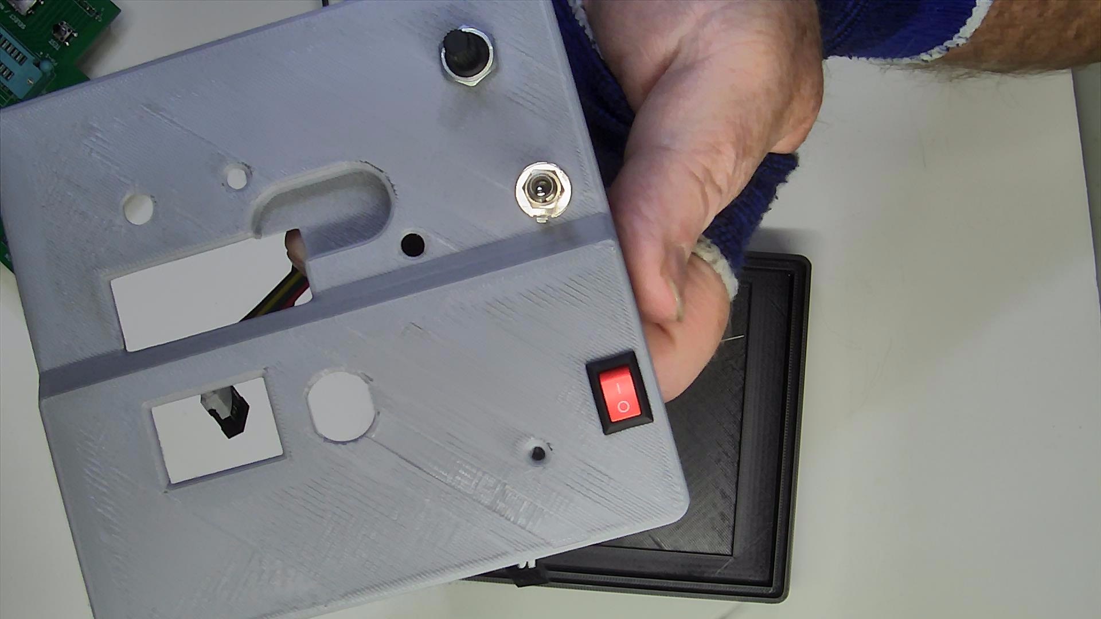
docs/images/build/53-top-case-close.jpg
