LS120nz/OD-PT74-IC-Tester/docs/images/build/54-baseboaed-cables-topcase.jpg

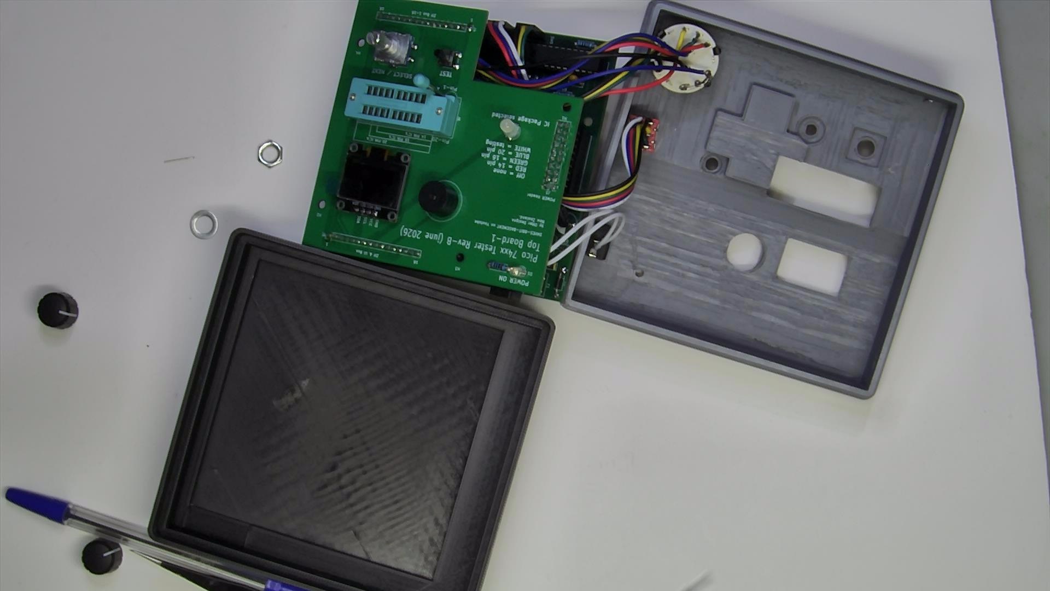
docs/images/build/54-baseboaed-cables-topcase.jpg
