LS120nz/OD-PT74-IC-Tester/docs/images/build/55-board-stack in case-base-with-top-case.jpg

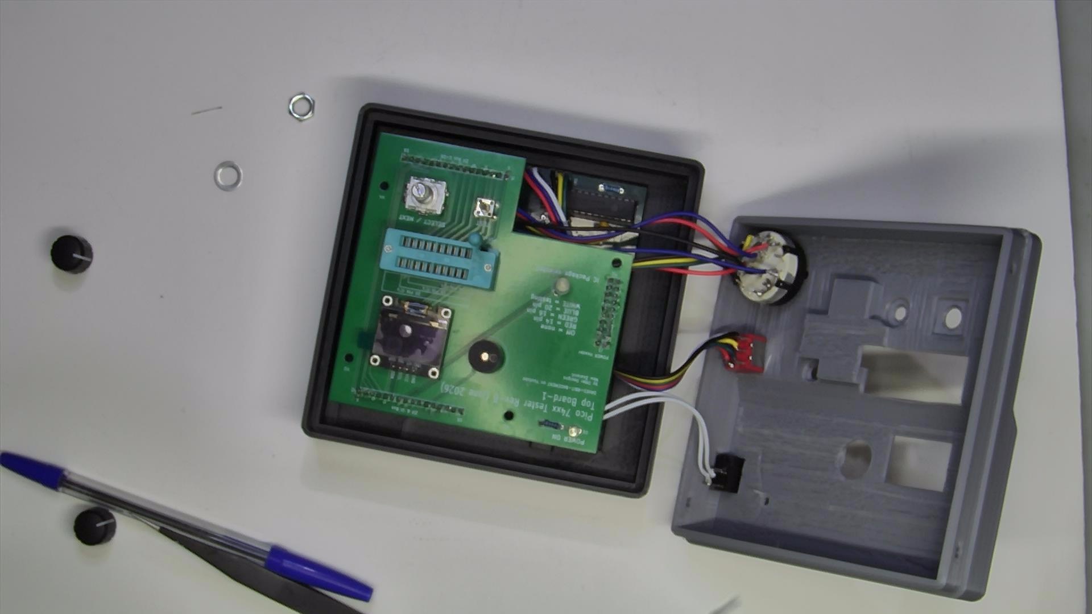
docs/images/build/55-board-stack in case-base-with-top-case.jpg
