LS120nz/OD-PT74-IC-Tester/docs/images/build/56-case-closed-finnished.jpg

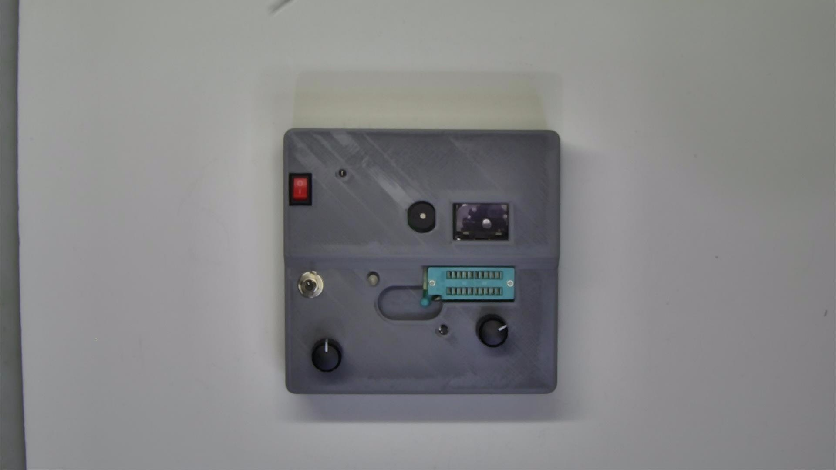
docs/images/build/56-case-closed-finnished.jpg
