LS120nz/OD-PT74-IC-Tester/docs/images/build/57-encoders-1.jpg

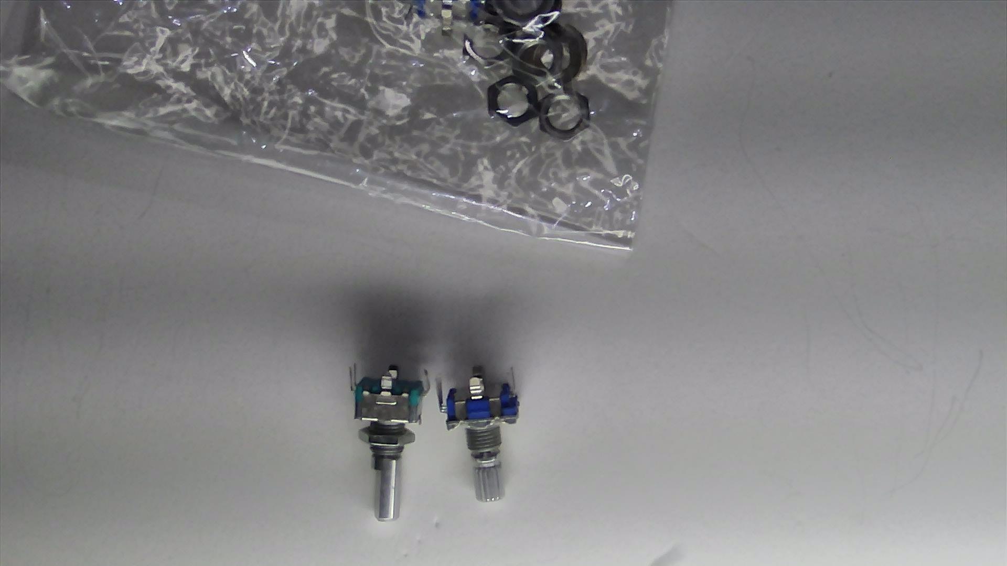
docs/images/build/57-encoders-1.jpg
