LS120nz/OD-PT74-IC-Tester/docs/images/build/61-selector-case-align-hole.jpg

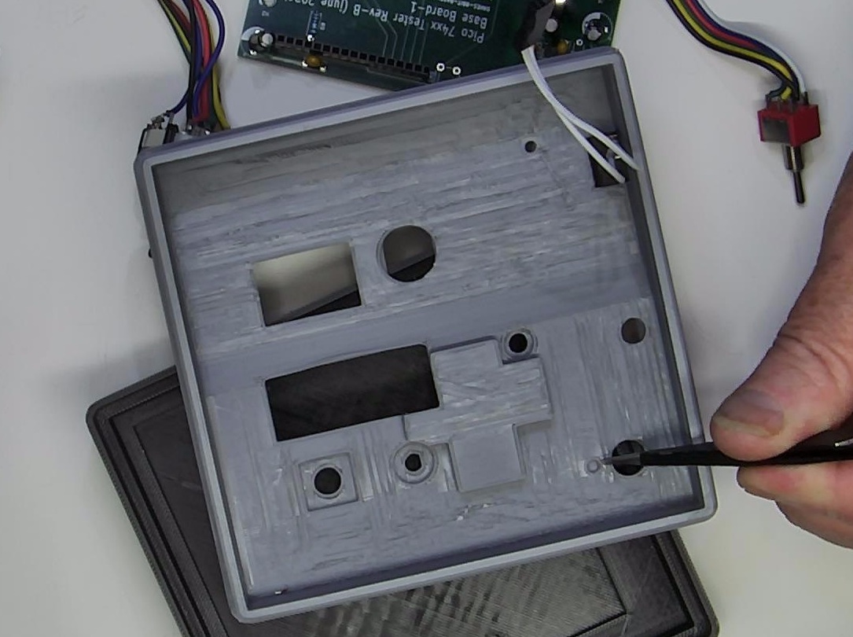
docs/images/build/61-selector-case-align-hole.jpg
