LS120nz/OD-PT74-IC-Tester/docs/images/build/62-selector-pin-dot.jpg

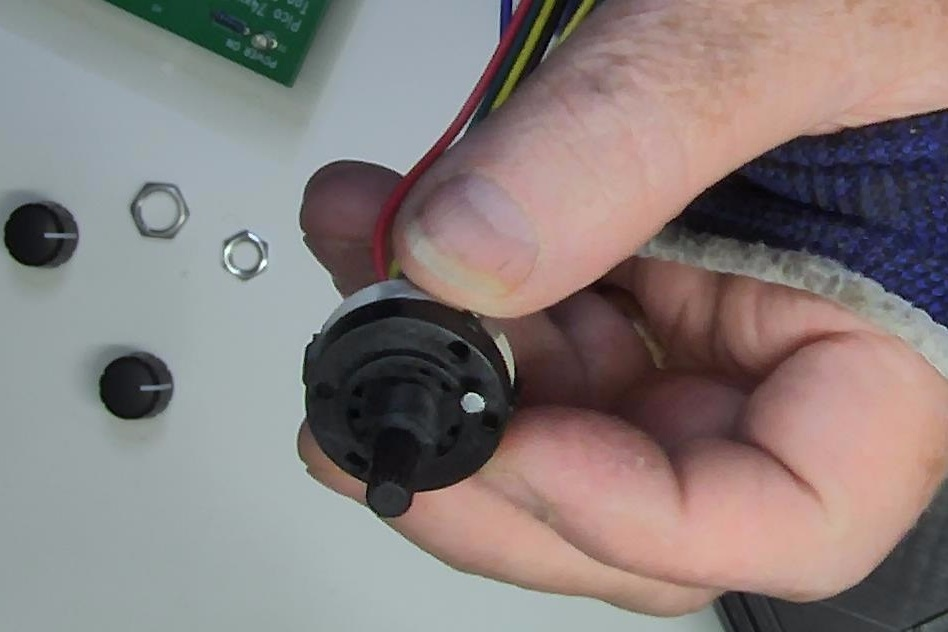
docs/images/build/62-selector-pin-dot.jpg
