LS120nz/OD-PT74-IC-Tester/docs/images/build/69- selector-pins.jpg

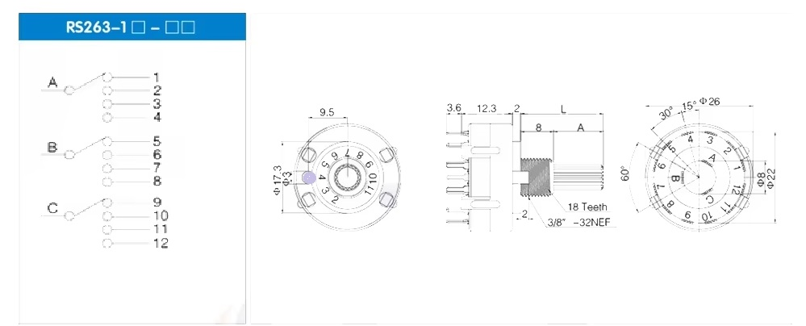
docs/images/build/69- selector-pins.jpg
