LS120nz/OD-PT74-IC-Tester/docs/images/build/angle-top.jpg

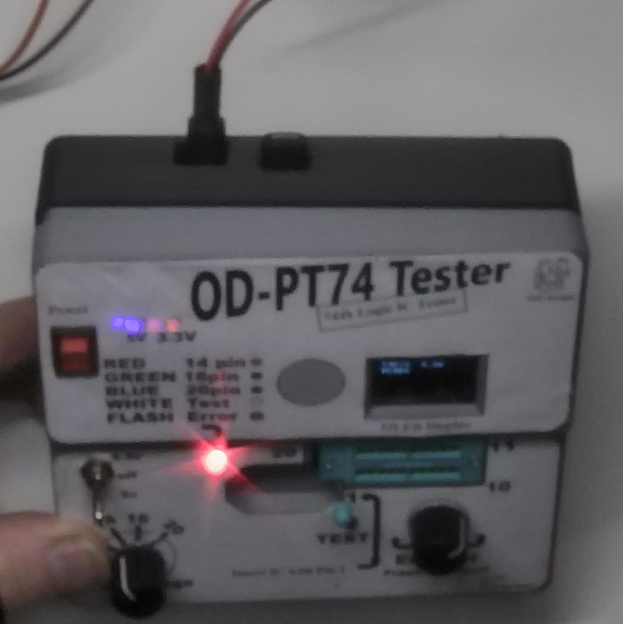
docs/images/build/angle-top.jpg
