LS120nz/OD-PT74-IC-Tester/docs/images/build/selector-side2.jpg

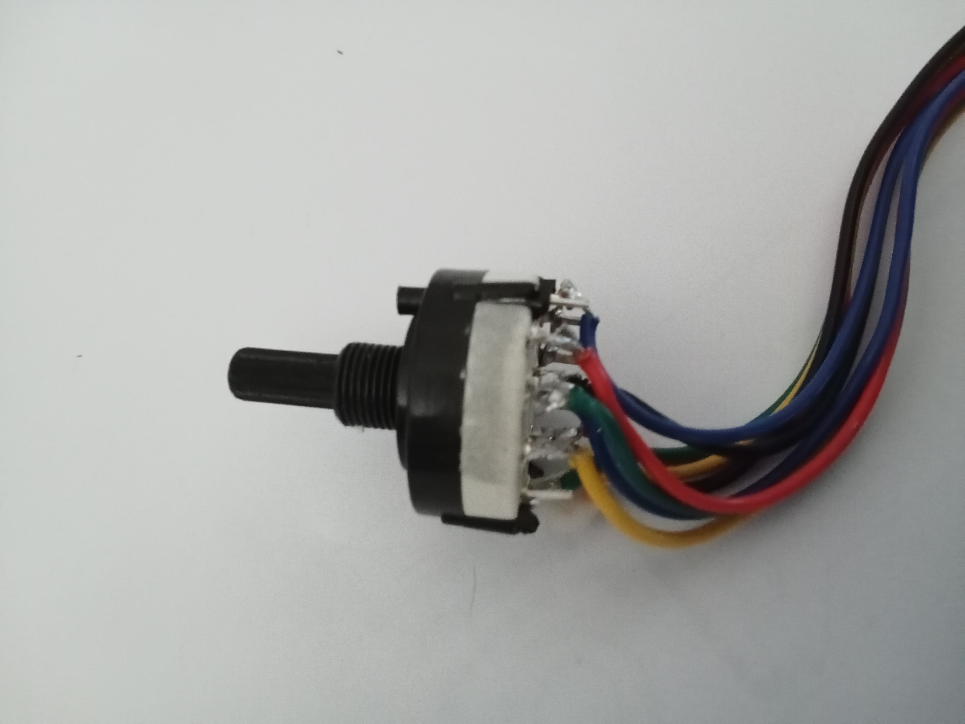
docs/images/build/selector-side2.jpg
