LS120nz/OD-PT74-IC-Tester/docs/images/build/usb-cable.jpg

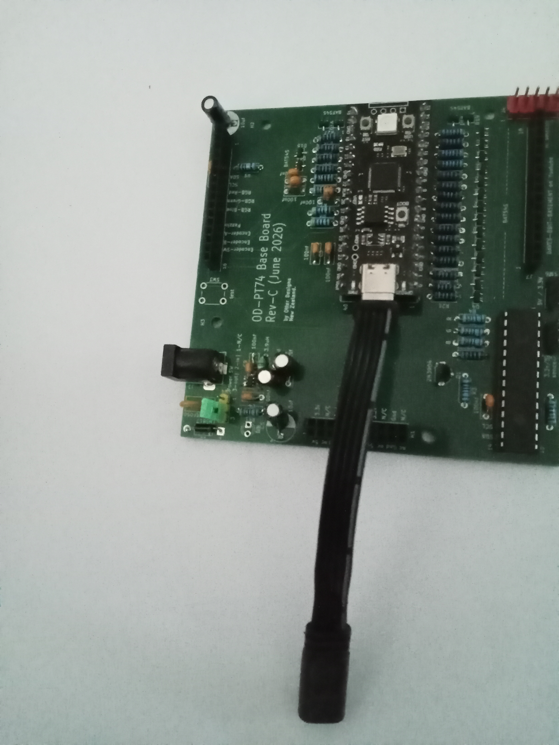
docs/images/build/usb-cable.jpg
