LS120nz/OD-PT74-IC-Tester/docs/images/build/voltage-switch2.jpg

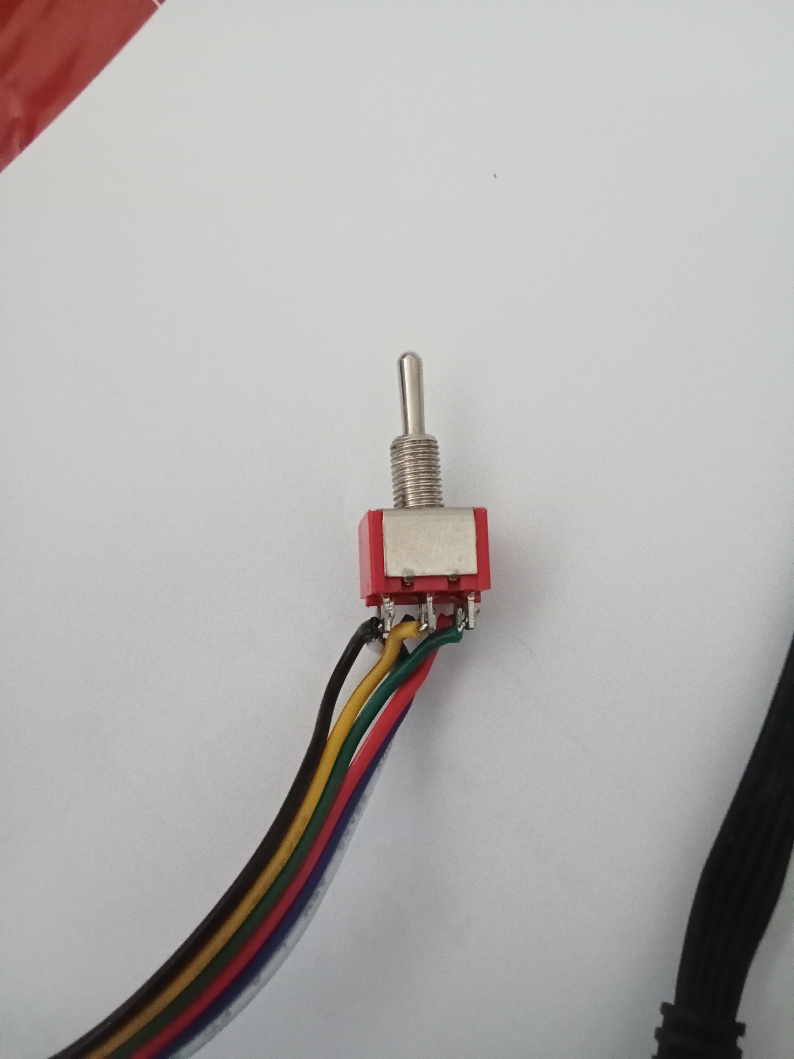
docs/images/build/voltage-switch2.jpg
