LS120nz/OD-PT74-IC-Tester/docs/release/pcbway-images/Assembled.jpg

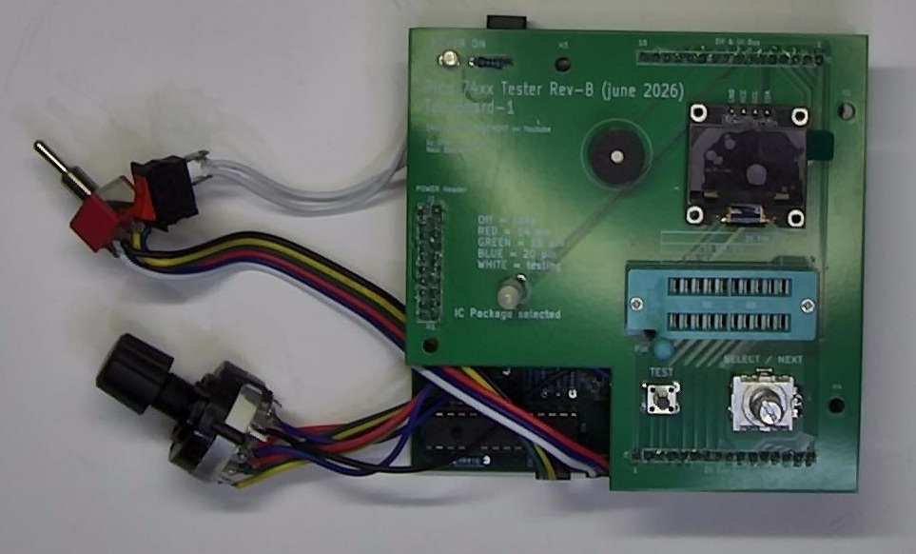
docs/release/pcbway-images/Assembled.jpg
