LS120nz/OD-PT74-IC-Tester/images/assembled.jpg

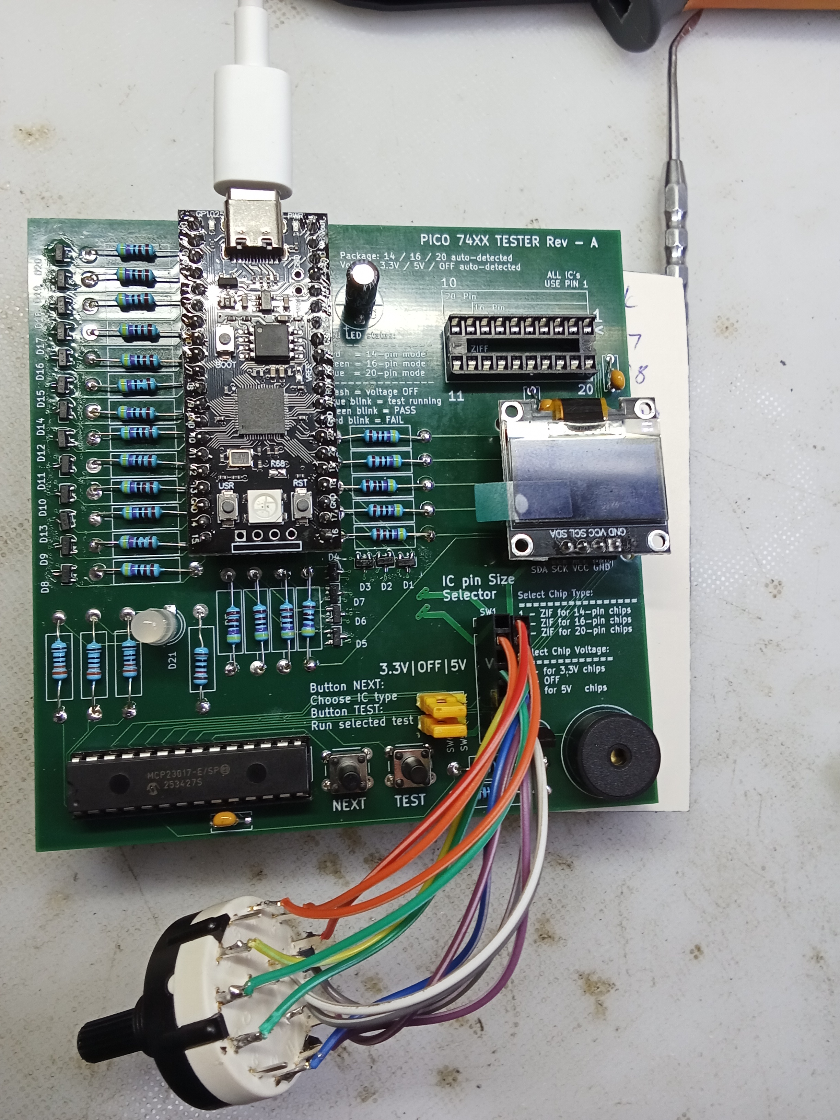
images/assembled.jpg
