LS120nz/OD-PT74-IC-Tester/docs/images/build/17-power-test-3v3-reg.jpg

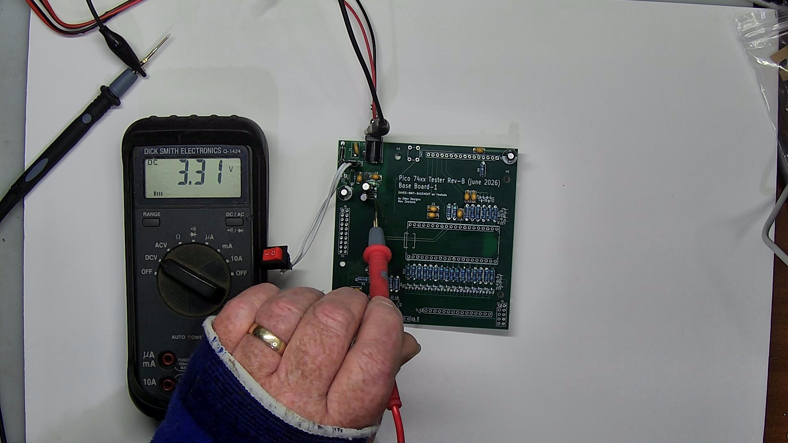
docs/images/build/17-power-test-3v3-reg.jpg
