LS120nz/OD-PT74-IC-Tester/docs/images/build/18-power-test-3v3.jpg

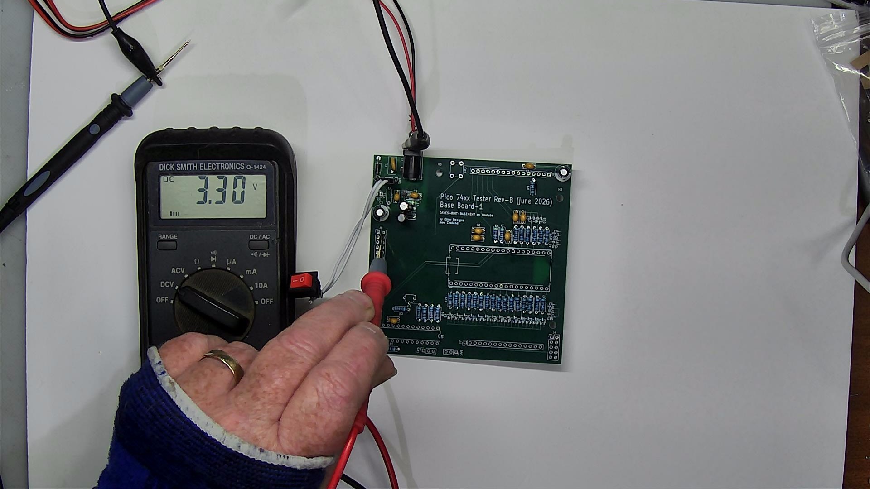
docs/images/build/18-power-test-3v3.jpg
