LS120nz/OD-PT74-IC-Tester/graphics/exports/figure-04-test-execution-flow.png

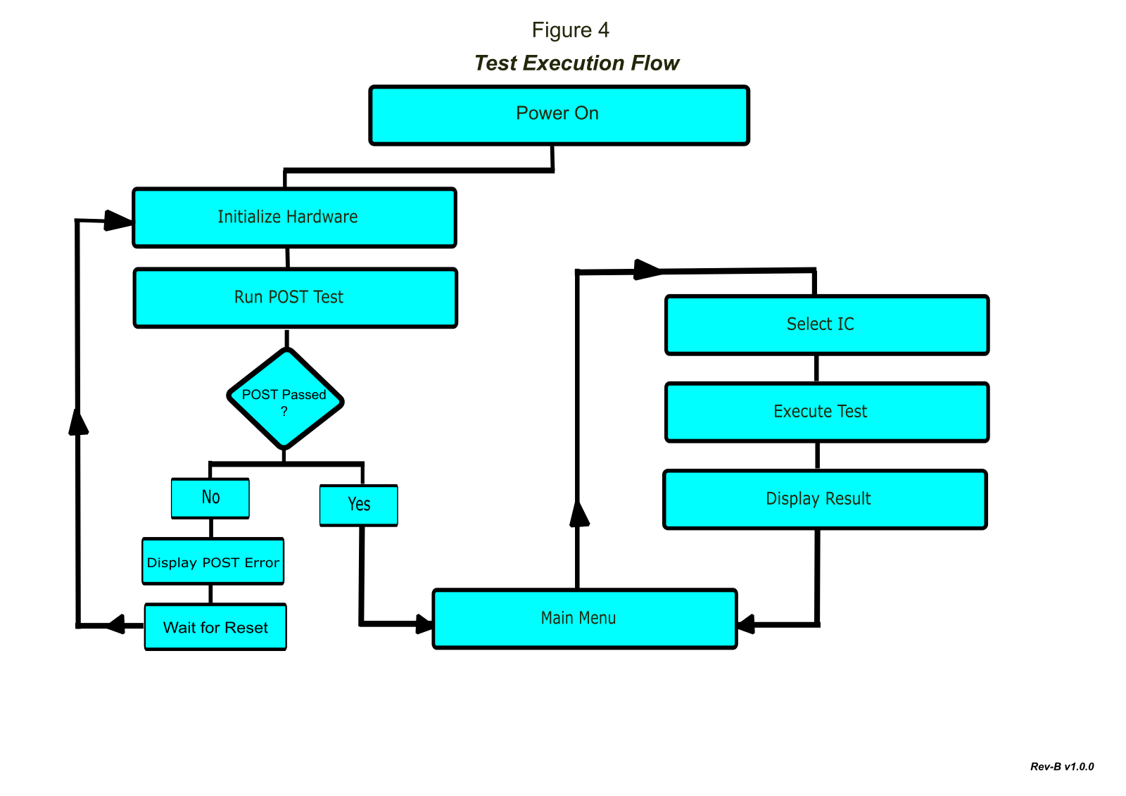
graphics/exports/figure-04-test-execution-flow.png
